ahsalohcin/GP-Team-8-/ihab/GrandPrIEEEE_2017-master/GrandPrIEEEE_2017-master/Natcar Docs/7-controller.pdf

### NATCAR – Background Information

### Steering Control-Loop Design Part I

Prof. Richard Spencer

### Outline

- The feedback-control problem
- PID Controllers
- Kinematic model of car
- Simulated response

### The Feedback Control Problem

- Remember the basic block diagram we had before:
- The “Plant” or “Process” is your car in this project
- The objective in designing the sensing and controller is to make the car follow the course in a well-behaved manner so that it can do so quickly
- You have two loops to design: steering and speed

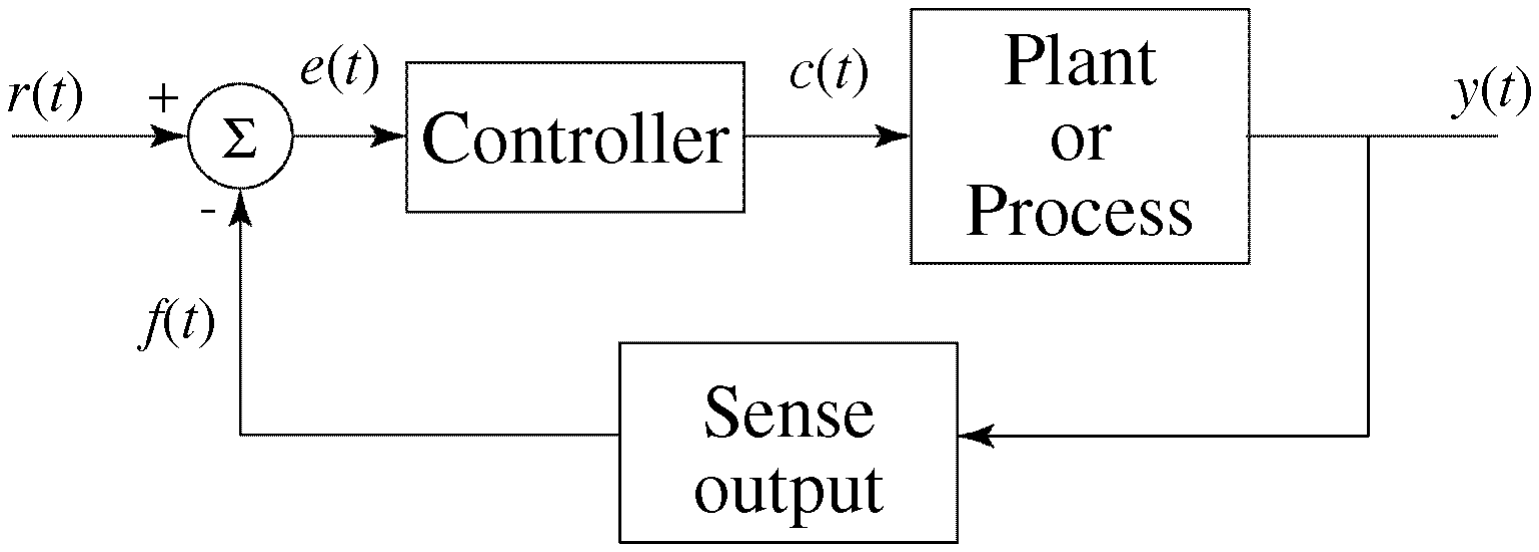
[picture p55: figure]

### Controller Design

- There are many types of controllers used to tailor the response of a control system. EEC157A,B discusses this topic at length.
- We will only examine one very general form for the controller; a Proportional + Derivative + Integral (PID) controller.
- The controller output is simply given by the sum of three terms:
– Proportional;

– Integral;

– Derivative;

( ) | ( ) p ct | ket =
( ) | ( ) pd c t | k T de t dt = | ⎡ | ⎤ ⎣ | ⎦

()

0

()

t
p

i

k
ct | e | d
T = | λλ ∫

### PID Controller

- The controller transfer function is
- The loop gain is then the product of the transfer functions of the controller, the plant and the sensing system.
- Let’s derive a model for our “plant”, which is the car. Then we’ll return to examine the design of an appropriate controller. We will focus here on the steering control loop – it is BY FAR the most important (the fastest car to date had a fixed speed).
() | ( ) ()
1 1 c | p | d

i

Cs
H s | k | sT
E s | sT
⎛ | ⎞
= | = | + | + ⎜ | ⎟ ⎝ | ⎠

### Kinematic Model for the Car

- Because the traction is very good and the tires don’t deform much, we can use a kinematic model (i.e., ignoring mass and force) instead of a full dynamic model for the car.
- We will assume a constant velocity, but the results are fine so long as the velocity doesn't change too rapidly.
- When we have the model in the Laplace domain, we can then build a Matlab (or even SPICE) model for the car and simulate the performance of the car with a given controller design.

- Assume small θ and φ and that the car is moving with constant velocity v. Write equations for the position of the center of the rear axle.
- First:

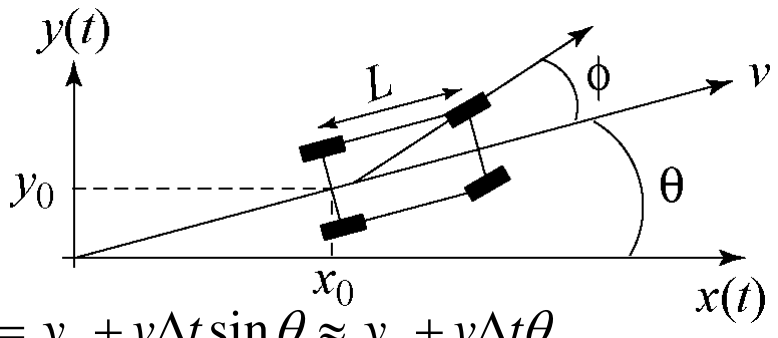
[picture p56: figure]

then,
- Second:
so,
0 | 0 y t | y vt | y vt ( ) | sin Δ = +Δ | ≈ +Δ θ | θ
y dy dt v = | ≈ θ
0 | 0 x( ) | cos Δ = +Δ | ≈ +Δ t | x vt | x vt θ
x = dx dt v ≈

### Kinematic Car Model Continued

This model is
sometimes called
the bicycle model

x0 and y0 are the
positions at t = 0

### Use New Axes in Line with the Car

Assume both the back and front wheels move in the direction they are pointing (can’t be true). We want to find the change in car direction, Δθ. Define a new axis, y’, perpendicular to v

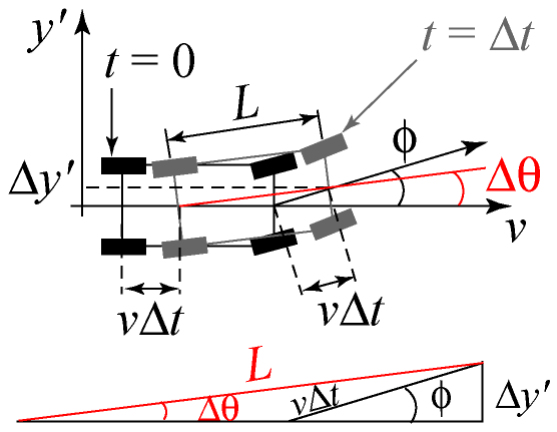
[picture p57: figure]

1 sin

sin

y | y
L | L
y vt | vt
vt
L

θ

φ φ
φ θ
− ⎛ | ⎞ Δ | Δ ′ | ′ Δ= | ≈ ⎜ | ⎟ ⎝ | ⎠
Δ =Δ | ≈Δ ′
Δ Δ≈

- Now write an equation for the y-component of the sensor position (taken to be at the center of the sensor array)

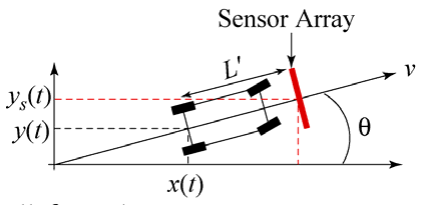
[picture p58: figure]

- Still assuming small θ , we have
- So,
( ) | ( ) | sin
| ()
s y | t | yt L
yt L

θ
θ

Δ= Δ+ ′
≈ Δ+ ′

### Kinematic Car Model Continued

() | () s y | t | yt L | v | L Δ≈ Δ+ | ≈ + ′θ θθ′ | |

### Put the Equations Together

We have | and
Therefore, | and, still assuming v is
constant,

so that, in the Laplace domain we have

s y | v | L ≈+ θ ′θ
| vt
L

φ θ Δ Δ≈

v
L

φ θ ≈

2

s

v | vL y | v | L | L | L
φ | φ θθ | ′ ≈+ | = | + ′ | |
2 | 2
2 | 2
1 | / () | () | () s
v | vL | v | sL v Ys | s | s
Ls | Ls | L | s
⎛ | ⎞ | ⎛⎞ ′ | ⎛ | ⎞ + ′ ≈ | + | Φ= | Φ ⎜ | ⎟ | ⎜⎟⎜ | ⎟ ⎝ | ⎠ | ⎝⎠⎝ | ⎠

### Model the System

The transfer function for the car is

Let’s assume that the servo is linear and model it by a single-pole LP transfer function

The overall model for our plant is then given by

()

2

2

() | 1 | /
()

s
car
Y s | v | sL v H | s
s | L | s
⎛⎞⎛ + ′ ⎞ = | = ⎜⎟⎜ | ⎟ Φ | ⎝⎠⎝ | ⎠

() ()
() 1

s k
Hs
Cs | s φ
φ | ωφ
Φ= | = +

()

| 2

2

() | 1 | /
() 1

s
p
Y s | v | sL v k
Hs
Cs | s | L | s
| φ
ωφ
⎛⎞⎛ + ′ ⎞ = | = | ⎜⎟⎜ | ⎟ + | ⎝⎠⎝ | ⎠

### System Model Continued

- Assume the sensors provide an output proportional
to the deviation from the track so that | .
- We now have a complete block diagram model of our control system.
– ys(t) is the sensor array deviation from the track (in feet) – r(t) is the reference input, which is zero
– T(t) is the racetrack; it provides deviations that the control loop must respond to.
( ) Hs | s s | k =

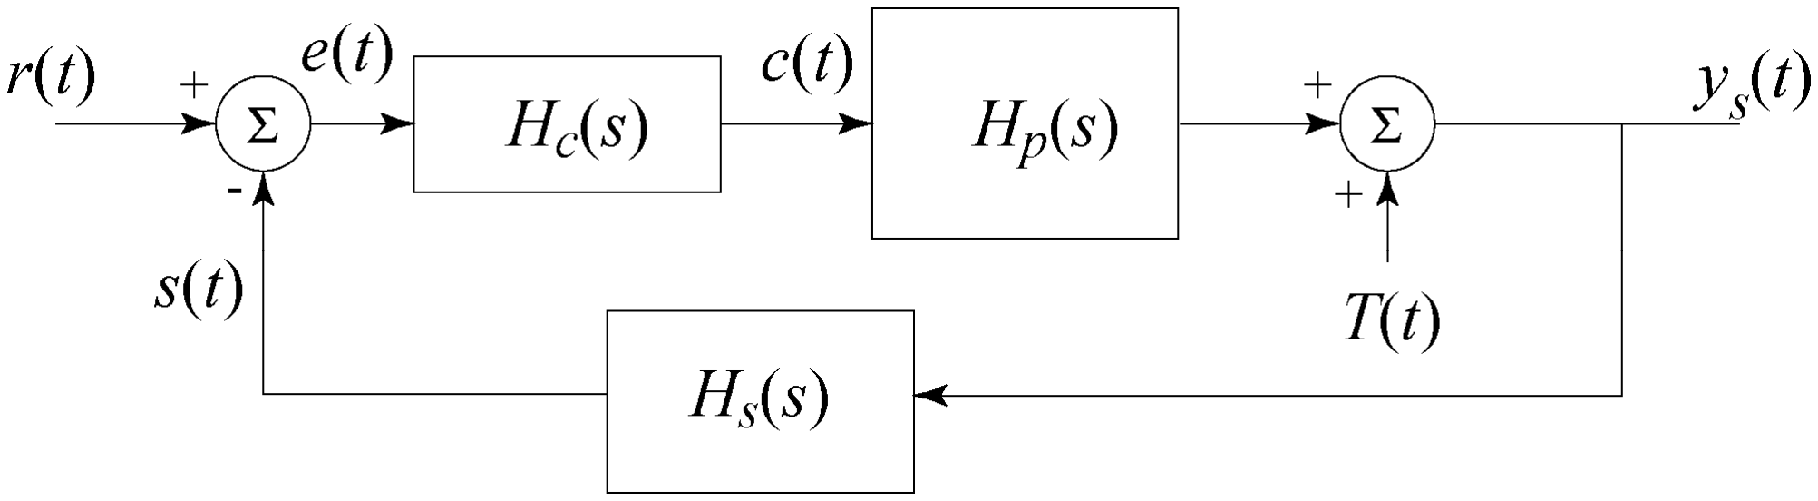
[picture p59: figure]

### System Model Continued

- Since r(t) = 0, we can redraw the loop with the track as the input.

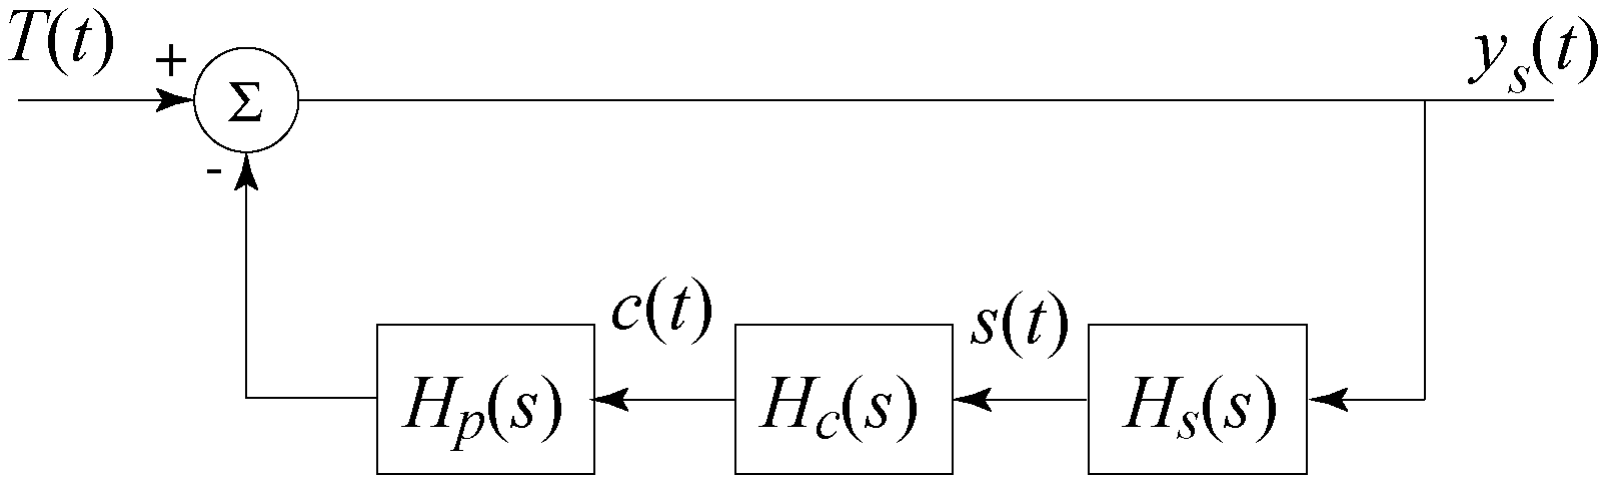
[picture p60: figure]

- Using the equations we’ve derived, we have
( ) ( ) ( ) ( )

2

2

1 | 1 | / 1
1
s | c | p
sp | d
i
Ls | H sH sH s
k | v | sL v k k | sT
sT | s | L | s

φ
ωφ

=
⎛ | ⎞ | ⎛⎞⎛ + ′ ⎞ = | + | + ⎜ | ⎟ | ⎜ ⎜⎟ | ⎟ ⎝ | ⎠ + | ⎝⎠⎝ | ⎠

### System Model; Example Numbers

- Assume the following:
– The sensor gain is one (V/ft)
– The servo gain is π/2 = 1.57 (rad/V)
– The servo bandwidth is 100 rad/sec
– The wheelbase is L = 1 foot and L’ = 1.5 feet
– The velocity is 5 ft/sec
– The controller is proportional only with a gain of one (V/V)
- Let’s use Matlab to generate the Bode plots, a Nyquist plot of L, and the step response for the closed-loop system with a proportional-only controller

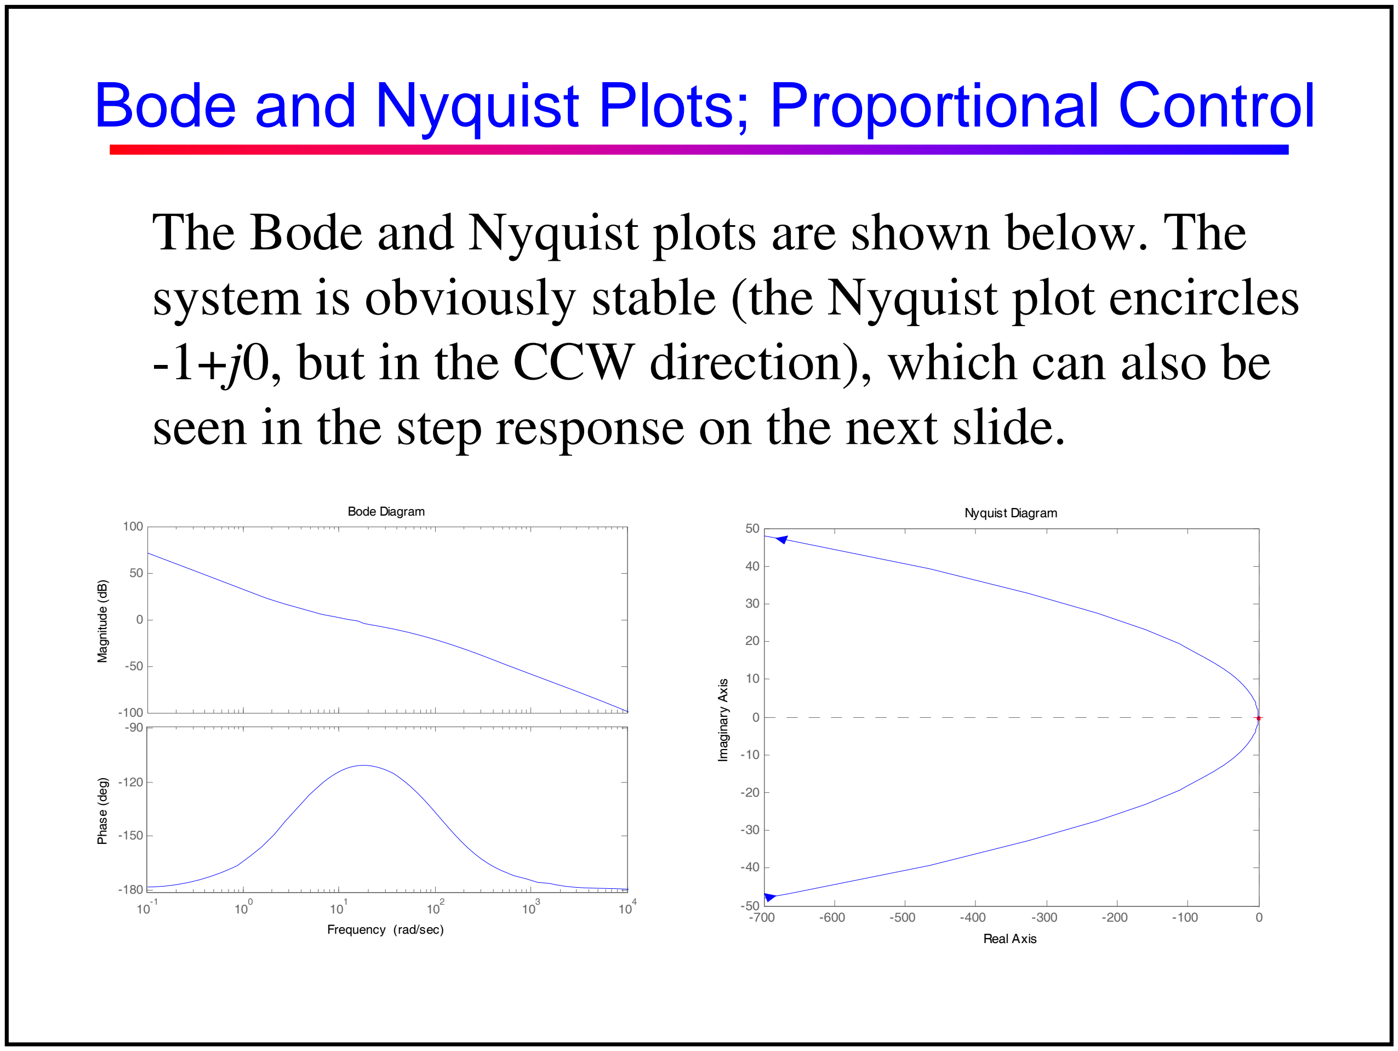
[picture p61: figure]
Magnitude (dB); Phase (deg); Bode Diagram; Frequency (rad/sec); Nyquist Diagram; Real Axis; Imaginary Axis

Bode and Nyquist Plots; Proportional Control

The Bode and Nyquist plots are shown below. The system is obviously stable (the Nyquist plot encircles -1+j0, but in the CCW direction), which can also be seen in the step response on the next slide.

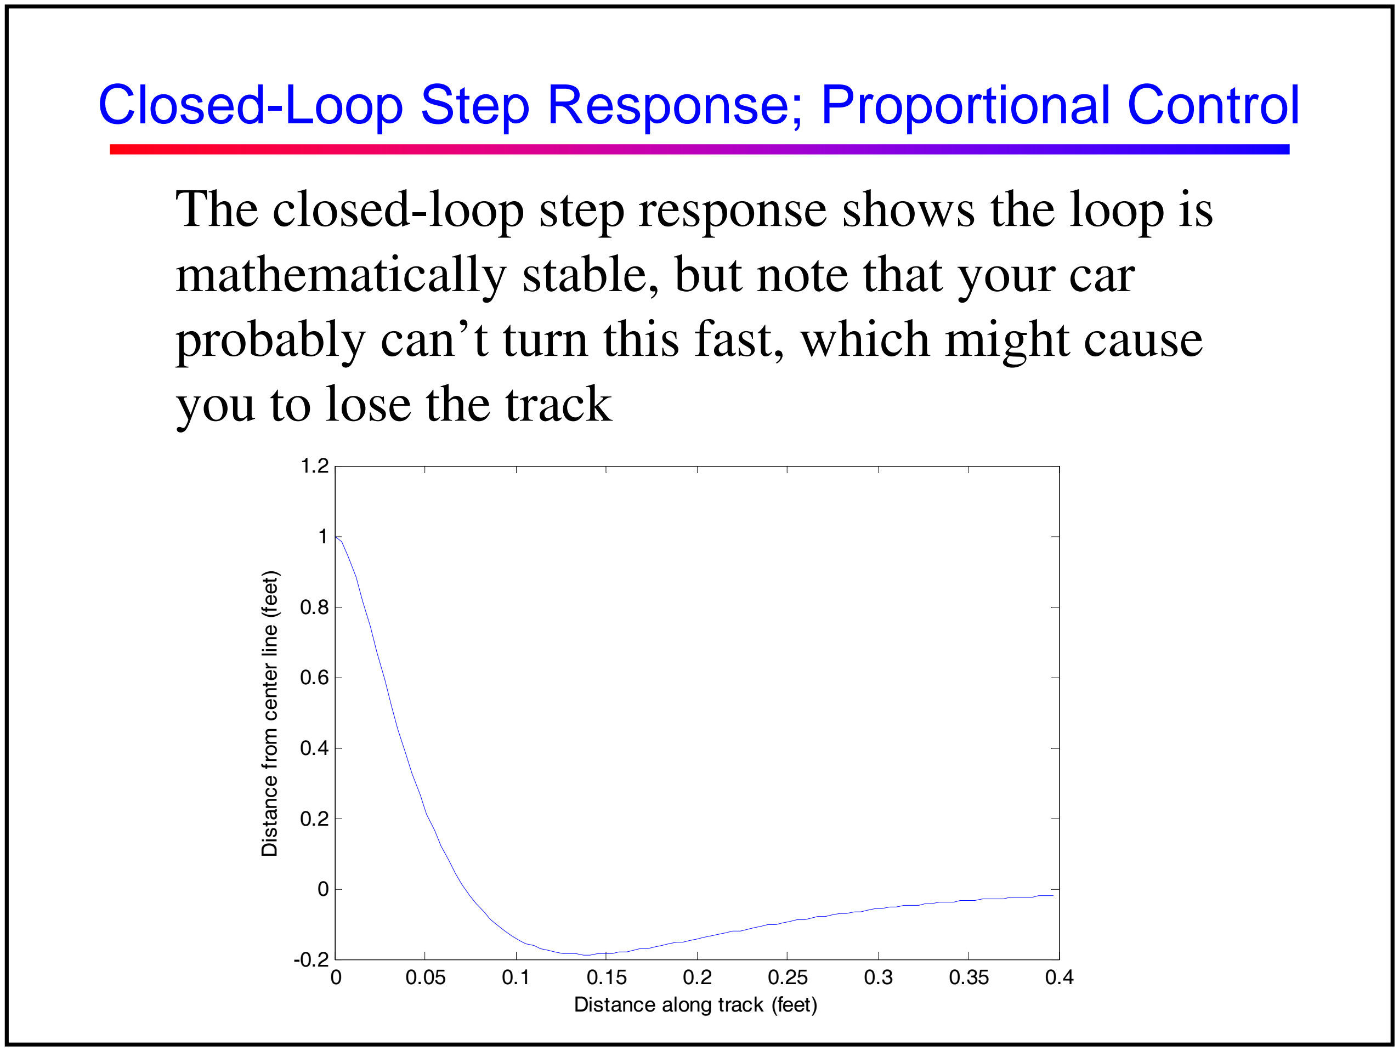
[picture p62: figure]
Closed-Loop Step Response; Proportional Control; you to lose the track; Distance along track (feet); Distance from center line (feet)

The closed-loop step response shows the loop is mathematically stable, but note that your car probably can’t turn this fast, which might cause

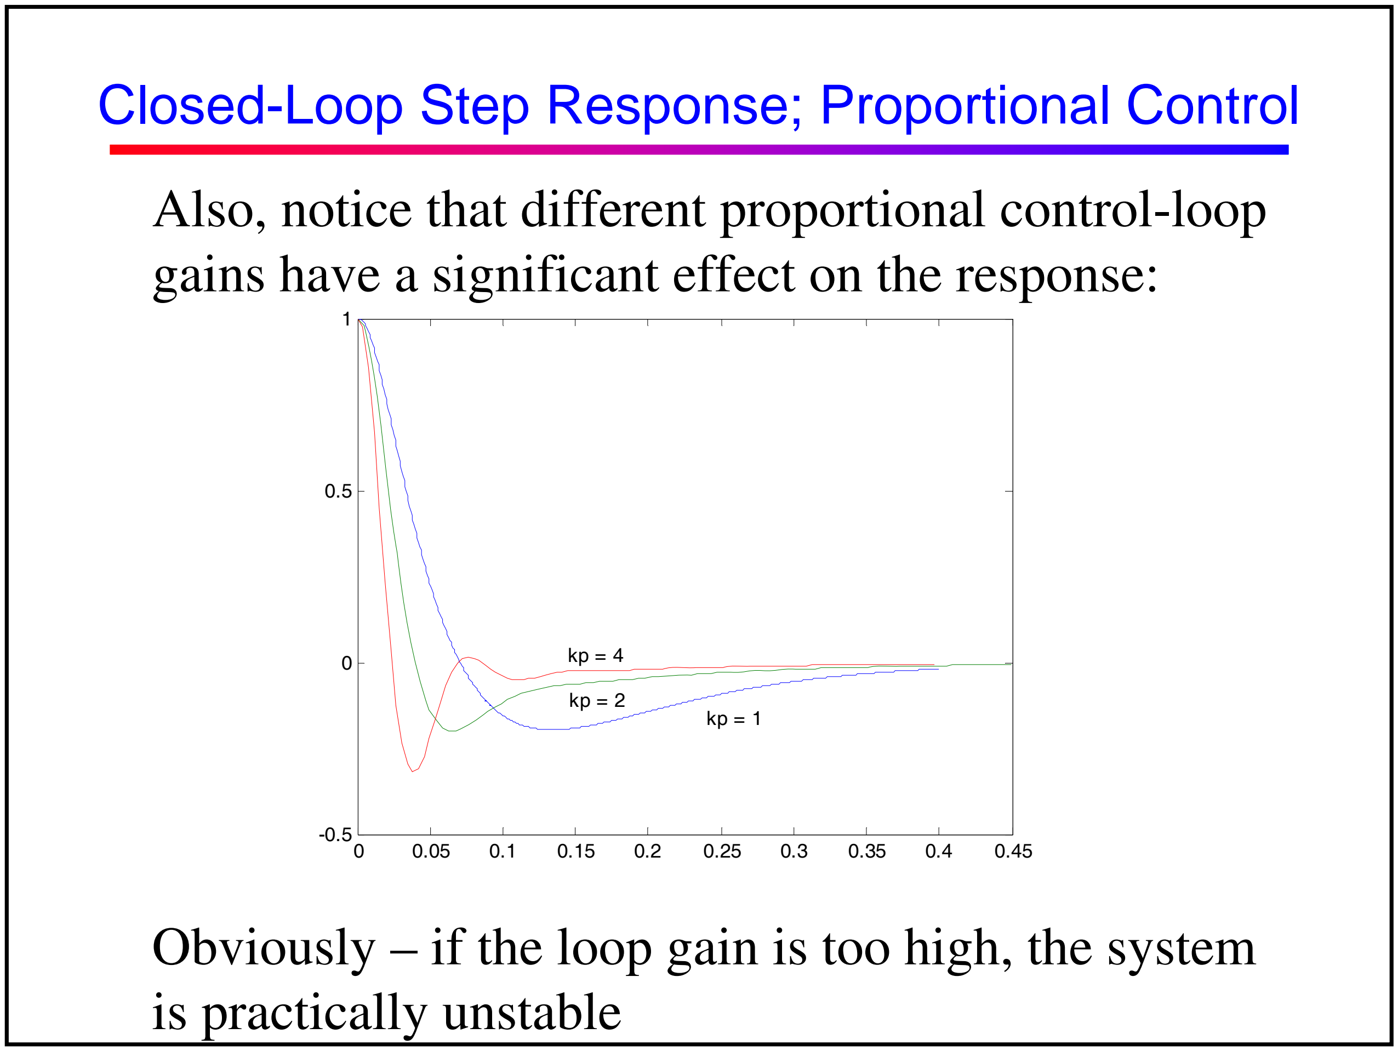
[picture p63: figure]
Closed-Loop Step Response; Proportional Control; is practically unstable

Also, notice that different proportional control-loop gains have a significant effect on the response:

Obviously – if the loop gain is too high, the system

### Re-Consider System Model

- Let’s reconsider our system model and see what we are ignoring
– The servo has a slew-rate limitation

### Servo Slew-Rate Limitation

- Slewing is a nonlinear phenomenon, so we can’t rigorously model it in the Laplace domain
- Nevertheless, servo slewing delays the steering response, and adding delay into the loop makes it less stable
- In addition, the slewing prevents the car from turning as quickly as our simulations sometimes show, which means that your car may run off the track and lose the signal entirely even if the control loop is theoretically stable

### Re-Consider System Model

- Let’s reconsider our system model and see what we are ignoring
– The servo has a slew-rate limitation
– The sensing transfer function may be nonlinear

### Nonlinear Sensing

- If the sensing transfer function is monotonic and reasonably smooth, then nonlinearity does not significantly affect stability
– if it had steps, that might cause problems because it would cause rapid changes in the steering and would drive the servo into a slewing mode more often
– if it was non-monotonic, then negative feedback would become positive feedback wherever the slope of the sensing transfer function changed sign and the loop could enter a local limit cycle

### Re-Consider System Model

- Let’s reconsider our system model and see what we are ignoring
– The servo has a slew-rate limitation
– The sensing transfer function may be nonlinear
– The steering servo is only controlled at discrete times, in other words, the steering angle is actually sampled and held (about every 3 ms)

### Sampling

- The control signal generated by your circuits, c(t), is continuous-time, but it controls a PW modulator and the value is only transferred to the steering servo once every period (about once every 3ms)
- Therefore, the servo functions as a sample-and-hold circuit; that is, it samples c(t) once a period and then holds that value until the next sample arrives
- Let’s consider this intuitively for a moment …

### Sampling Continued

- If the time samples are held, you get a waveform that looks like this

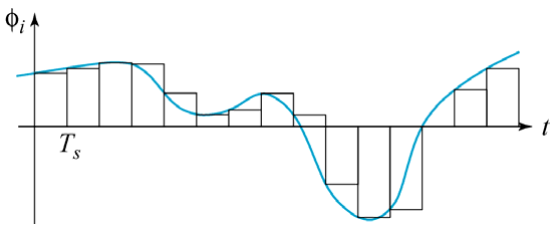
[picture p64: figure]

### Sampling Continued

- If the time samples are held, you get a waveform that looks like this
- Notice that if you reconstruct the original from the sampled-and-held version, it appears delayed!

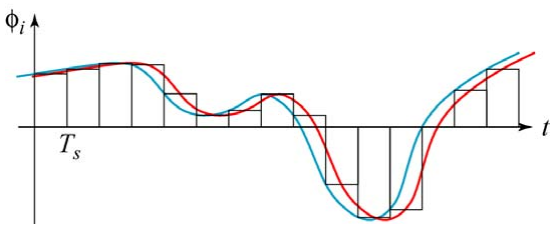
[picture p65: figure]

### Sampling Continued

- Adding delay into the loop is equivalent to adding in extra phase, so it tends to make the loop less stable

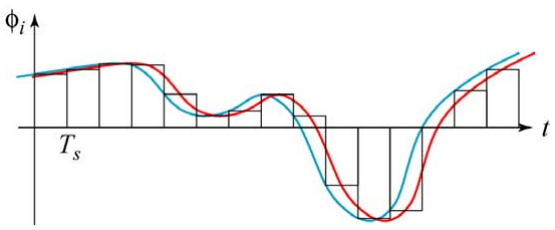
[picture p66: figure]
