ahsalohcin/GP-Team-8-/ihab/GrandPrIEEEE_2017-master/GrandPrIEEEE_2017-master/Natcar Docs/7B-PID-controller.pdf

### NATCAR – Background Information

### Steering Control-Loop Design Part II

Prof. Richard Spencer

### The System Model

Remember that the overall model for our plant is given by

The controller transfer function is

And we assumed the sensors have

()

2

2

() | 1 | /
() 1

s
p
Y s | v | sL v k
Hs
Cs | s | L | s
| φ
ωφ
⎛⎞⎛ + ′ ⎞ = | = | ⎜⎟⎜ | ⎟ + | ⎝⎠⎝ | ⎠
() | 1 1 c | p | d

i

H s | k | sT
sT
⎛ | ⎞
= | + | + ⎜ | ⎟ ⎝ | ⎠
Hs ( ) s s | k =

### The System Model Continued

- Also remember that the servo only samples the control voltage (about every 3ms) and then holds the value until it gets the next sample, so its input is really the sampled-and-held version of the control output, which we showed last time is roughly equivalent to adding some delay (~TS/2) into the loop

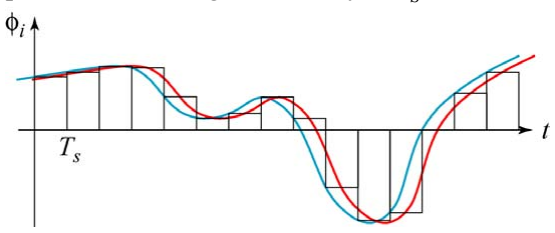
[picture p67: figure]

### Aside on Sampling

- We now want to quickly look at how to model this sample-and-hold operation mathematically
- The sample-and-hold function can be broken down into two separate functions; ideal impulsive sampling followed by a hold function
- Ideal sampling can be described mathematically by multiplying the waveform by a periodic string of impulses s(t):
() | ( | )

k

s t | t kT δ

∞

=−∞

= − ∑

### Sampling Continued

- Therefore, if we sample some waveform x(t) and denote the sampled waveform by x’(t) we find
- The Fourier transform of this infinite comb of impulses, s(t), is itself an infinite comb of
impulses, S(ω):
() | () () | () ( | ) | ( ) ( | )
k | k
x t | x t s t | x t | t kT | x kT t kT δ | δ
∞ | ∞
=−∞ | =−∞
′ = | ⋅ | = | − | = | − ∑ | ∑
2 () | ( | )s

k

S | k
T

π
ω | δω ω

∞

| =−∞
= | − ∑

### Sampling Continued

- Multiplication in the time domain implies convolution in the frequency domain, so we find:
1 | 1 () | () | () | ( | ) 2 | s

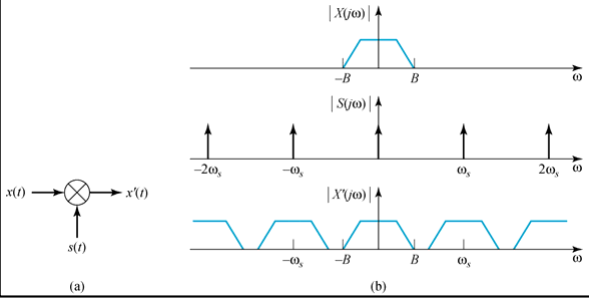
[picture p68: figure]

k

X | X | S | X | k
T
ω | ω | ω | ωω
π

∞

=−∞

′ | = | ∗ | = | − ∑

### Sampling Continued

- So long as the sampling frequency, ωs, is more than twice the signal bandwidth, B, we can recover the signal by low-pass filtering the sampled waveform (B is sometimes called the Nyquist frequency, so ωs must be > 2·ωNyquist)

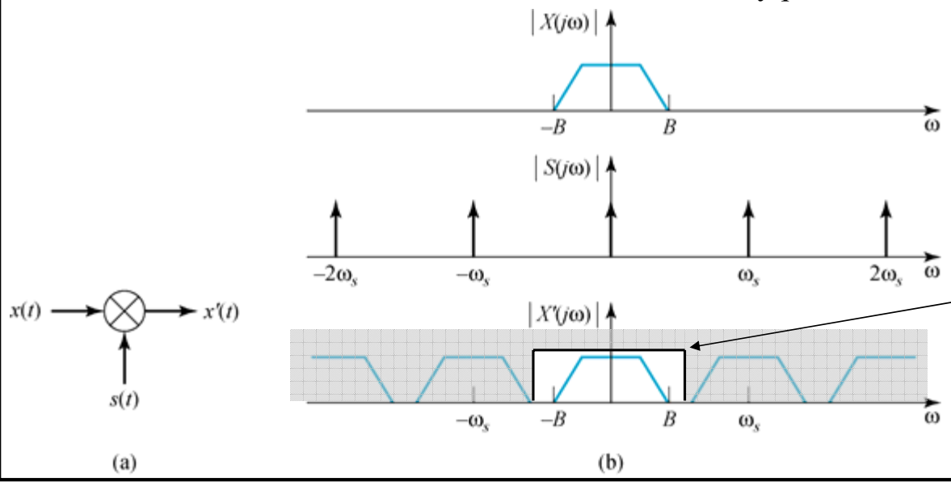
[picture p69: figure]

Ideal LPF

### Sampling Continued

- If the time samples are held, you get a waveform that looks like this:

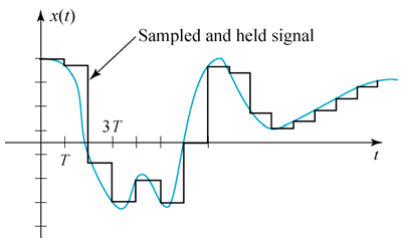
[picture p70: figure]

- This can be generated mathematically by convolving the sampled signal x’(t) with a pulse

### Sampling Continued

- Assuming we have a pulse p(t) defined by
- We find the sampled-and-held waveform is
- The Fourier transform of p(t) is
() | () | () | ( ) ( | ) SH

k

x t | x t p t | x kT p t kT

∞

=−∞

= | ∗ | = | − ′ | ∑
0; | 0 or () | 1;0
t | tT
pt | tT
⎧ | < | > = ⎨
⎩ | <<

0

1 ( ) | ()
T j t | jT
jt | e | e P | e p t dt | j | j
ω | ω
ω ω
ω | ω
∞ | − | −
−

−∞

⎡ | ⎤ − | − = | = | = ⎢ | ⎥ ⎣ | ⎦ ∫

### Sampling Continued

- We had
- And we had
- Therefore, their spectra are multiplied in the frequency domain and we have
() | () | () | ( ) ( | ) SH

k

x t | x t p t | x kT p t kT

∞

=−∞

= | ∗ | = | − ′ | ∑
() | () () X | X | P SH ω = ′ ω | ω ⋅

1 ()

j T
e P
j

ω
ω
ω

− − =

### Sampling Continued

- Note that
- And we had
2 | 2 | 2 | 2
2 | 2
1 | 2 | 2 ( ) | sin 2 | 2

sin
2 | sinc
2
2
T | T | T | T j | j | j | j jT
T | T j | j
e | e | e | e | e | T P
j | | | j
| T
T Te | Te T
ω | ω | ω | ω
ω
ω | ω

ω
ω
ω | ω | ω

ω
ω
ω
− | − | − −
− | −
⎛ | ⎞ − | − ⎜ | ⎟ = | = | = ⎜ | ⎟
⎝ | | | | | | ⎠
= | =
1 () | ( | )s

k

X | X | k
T
ω | ωω

∞

=−∞

′ | = | − ∑

### Sampling Continued

- Therefore,

2

2

1 ( ) | ( ) ( ) | ( | ) | sinc 2
sinc | ( | ) 2

T j

SH | s
k
T j

s
k
T X | X | P | X | k | Te
T
T e | X | k

ω

ω

ω
ω | ω ω | ωω
| ω | ωω
∞ | −

=−∞
∞ −

=−∞

⎡ | ⎤ = | ⋅ | = | − ′ | ⎢ | ⎥ ⎣ | ⎦
= | −

∑
∑

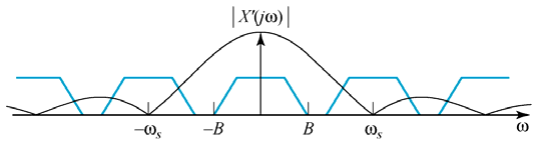
[picture p71: figure]

### Sampling Continued

- Note that if we focus on the region around zero (because we will low-pass filter the output), we can restrict our attention to the k = 0 term,
1 () | () () | ( | ) ()
| 1 ( ) ( ) | ( ) ( ) for | 0
SH | s
k
X | X | P | X | k | P
T
X | P | X | P | k
| T
ω | ω | ω | ωω | ω
ωω | ω ω

∞

=−∞

⎡ | ⎤ = | ⋅ | = | − ′ | ⎢ | ⎥ ⎣ | ⎦
= | ≡ | = ′

∑

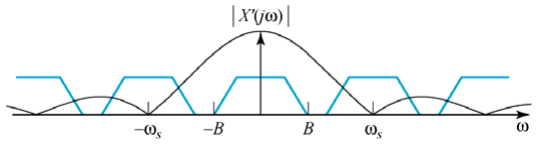
[picture p72: figure]

### Sampling Continued

- In other words, the sample-and-hold transfer function has a strange low-pass transfer charac-teristic that we must allow for in our simulations
- We do not need to model the actual sampling operation if we use a continuous-time model and assume that the sampling frequency is high enough (since we can perfectly reconstruct the signal)
- In the Laplace domain, we have
- This particular type of hold is called a zero-order hold (higher-order holds do a better job of interpolating between adjacent samples)

1 ()

sT
e Ps
sT

− − ′ =

### Simulation Model for the Loop

- But, we can’t enter the zero-order hold directly into Matlab as a transfer function – it won’t allow the perfect delay represented by the exponential (unless we do a discrete-time approximation to the entire control system in the z domain)
- An alternative to using MATLAB is to model the loop using SPICE – this method also has the advantage of allowing us to model nonlinearities
- The Laplace blocks available in PSPICE work in the frequency domain, but not in the time domain – so we must use controlled sources and elements to build up a behavioral model of the system

### PSPICE Car Model

- The transfer function for the car is

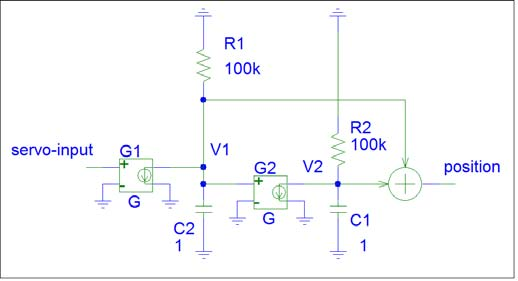
[picture p73: figure]

- We can model this in PSPICE with this circuit
2 | 2
2 | 2
1 | / () | () | () s
v | vL | v | sL v Ys | s | s
Ls | Ls | L | s
⎛ | ⎞ | ⎛⎞ ′ | ⎛ | ⎞ + ′ ≈ | + | Φ= | Φ ⎜ | ⎟ | ⎜⎟⎜ | ⎟ ⎝ | ⎠ | ⎝⎠⎝ | ⎠

### PSPICE Car Model Continued

- Ignore R1 and R2 at first – PSPICE requires them, but they don’t affect the operation much. So

and

- Therefore,

1
1
1
() | () in
G Vs | V s
sC
− = | 2 | 12
2 | 1 | 2
| 2 | 12
() | () | () in
G | GG V s | Vs | V s
sC | s C C
− = | =
12 | 1
1 | 2 | 2 () | () | () | () o | in
GG | G V s Vs V s | V s
s | s
⎛ | ⎞ = | + | = | − ⎜ | ⎟ ⎝ | ⎠

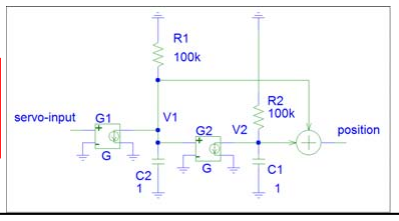
[picture p74: figure]

Note that both
capacitors are
1 Farad

### PSPICE Car Model Continued

- Setting Vin = Φ and Vo = Y, we have
- which requires | and 1

vL G
L

− ′ =

2
12 | 1
2 | 2 () | () | () s
v | vL | G G | G Ys | s | s
Ls | Ls | s | s
⎛ | ⎞′ | ⎛ | ⎞ ≈ | + | Φ= | − | Φ ⎜ | ⎟ | ⎜ | ⎟ ⎝ | ⎠ | ⎝ | ⎠

2

v G
L

− = ′

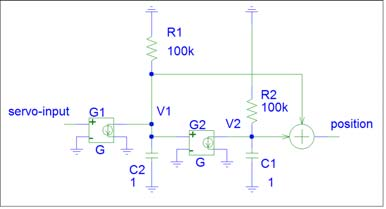
[picture p75: figure]

### PSPICE Servo Model

- The servo can be modeled in PSPICE as shown below – this model includes the servo slew rate, small-signal bandwidth and limits
- The first block has negative feedback, so

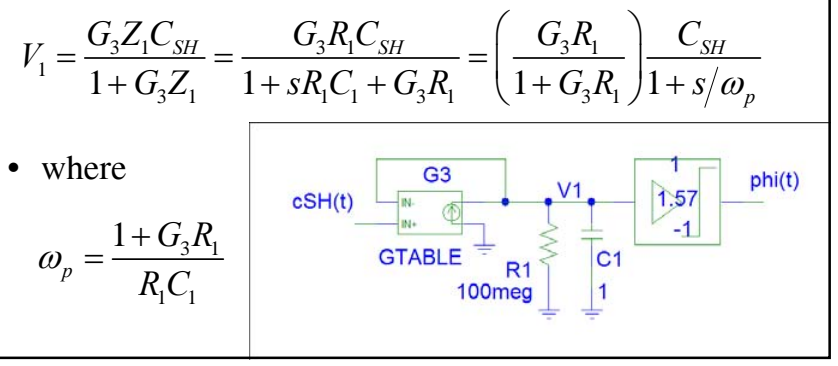
[picture p76: figure]
• where

### PSPICE Servo Model

- The slew rate is set by the maximum current available out of the GTABLE block; assuming it all flows into C1, the maximum rate of change of V1 is
- The steering limits are given by the voltage limit block, and the overall DC gain is also set by this block since we set
1 | max
max | 1
dV | I
dt | C =

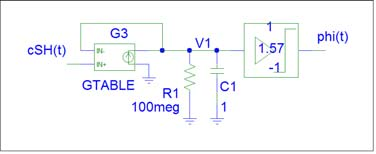
[picture p77: figure]

31

31

1
1

GR
GR
⎛ | ⎞
⎜ | ⎟ ≈
⎝ | ⎠ +

### PSPICE Zero-Order Hold Model

- The zero-order hold can be modeled using an ideal transmission line to provide the delay
- The transmission line must be terminated properly to prevent reflections – I used a 100Ω line with a 3ms delay (T1 in the schematic)
- The integrator block provides the 1/s term
- The input gain includes a factor of 2 to allow for the divider formed by R2 and the line as well as the 1/T term

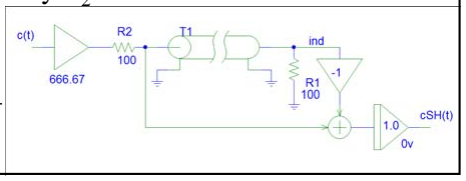
[picture p78: figure]

() | 1 () ()
sT Cs | e SH | Ps
C s | sT
− − = | = ′

### PSPICE Controller Model

- I modeled a PD controller as shown below
- The input gain block sets kp (10 in the schematic)
- The current in C1 is the derivative of kp·s(t), so the gain of the H1 block sets Td
- The output is the sum of the derivative and
proportional terms: c t | k | sT s t () | 1 | () = p | d ( + | )

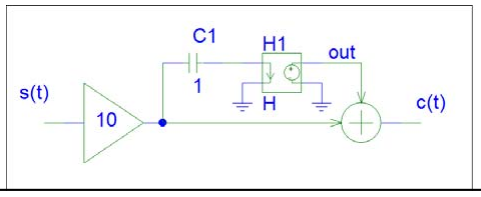
[picture p79: figure]

### Complete PSPICE Model

- The complete PSPICE model for the feedback loop is shown below
- The sensors are modeled by a gain block and the track by an independent source
- The gain of −1 is used to make the summer take the difference between Vin and the car’s position

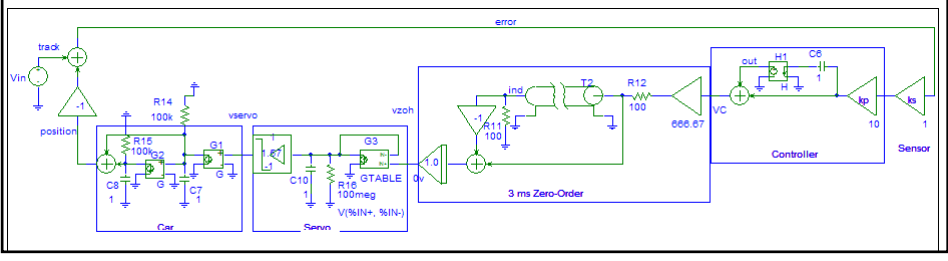
[picture p80: figure]

### System Model; Example Numbers

- Assume the following:
– The sensor gain is one (V/ft)
– The servo gain is π/2 = 1.57 (rad/V)
– The servo has a bandwidth of 100 rad/sec, a slew rate of 20 rad/sec (120º change in 0.1 sec) and limits of ±1 V (±60º) – The wheelbase is L = 1 foot and L′ = 1.5 feet
- Let’s use our PSPICE model to examine the step response for different velocities and controllers WARNING! You have to set the maximum step size in the transient simulations to a small value (I used 0.005ms most everywhere) and, perhaps, reduce the charge tolerance or you will not get accurate step responses

### Step Response

- Here is the step response (6 in. step) with kp = 1, Td = 0 s and v = 1 ft/s

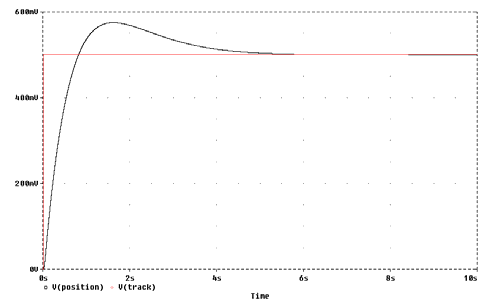
[picture p81: figure]

1 s = 1 foot

1V = 1 ft.

### Step Response

- Here is the step response (6 in. step) with kp = 10, Td = 0 s and v = 1 ft/s. Note the change in x axis scale and that this has less overshoot than kp = 1!

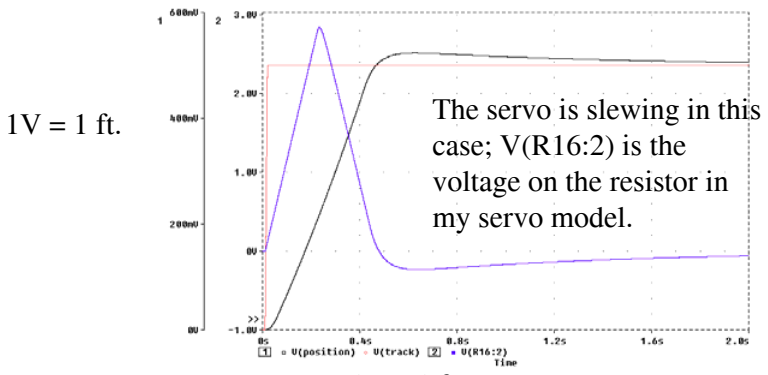
[picture p82: figure]
The servo is slewing in this; case; V(R16:2) is the voltage on the resistor in my servo model.

1 s = 1 foot

### Step Response

- Here is the step response (6 in. step) with kp = 1, Td = 0 s and v = 5 ft/s

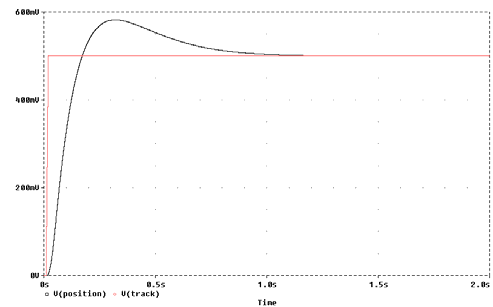
[picture p83: figure]

200 ms = 1 foot

1V = 1 ft.

### Step Response

- Here is the step response (6 in. step) with kp = 10, Td = 0 s and v = 5 ft/s. The servo is again slewing. The loop is, in practice, unstable.

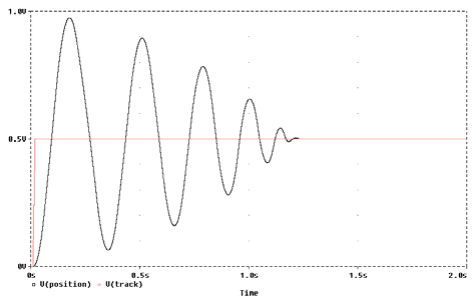
[picture p84: figure]

200 ms = 1 foot

1V = 1 ft.

### Step Response

- Here is the step response (6 in. step) with kp = 10, Td = 0.3 s and v = 5 ft/s. The derivative has helped a lot!

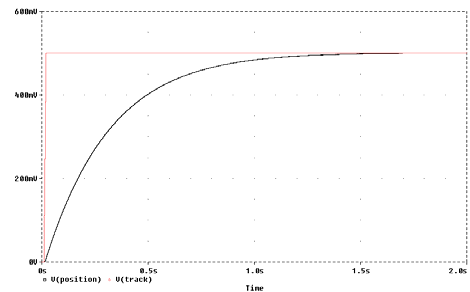
[picture p85: figure]

200 ms = 1 foot

1V = 1 ft.

### Step Response

- Here is the step response (6 in. step) with kp = 1, Td = 0 s and v = 10 ft/s

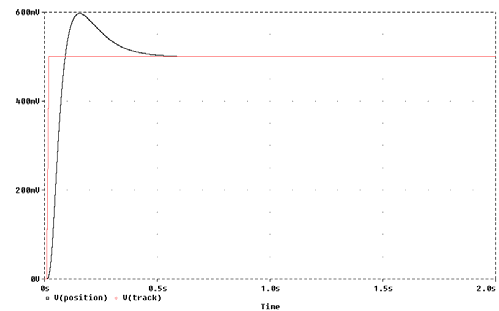
[picture p86: figure]

100 ms = 1 foot

1V = 1 ft.

### Step Response

- Here is the step response (6 in. step) with kp = 10, Td = 0 s and v = 10 ft/s. The loop is unstable here!

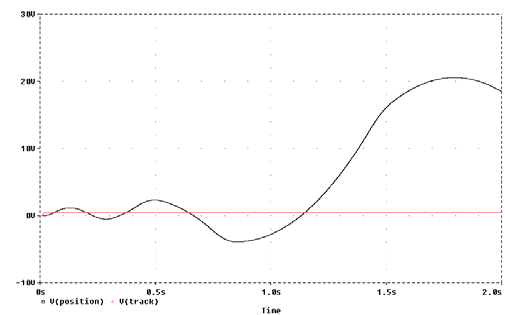
[picture p87: figure]

100 ms = 1 foot

1V = 1 ft.

### Step Response

- Here is the step response (6 in. step) with kp = 10, Td = 0.3 s and v = 10 ft/s. The derivative has again cured the instability.

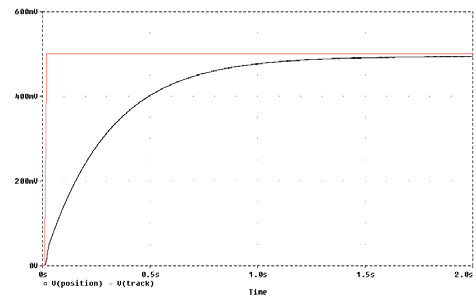
[picture p88: figure]

100 ms = 1 foot

1V = 1 ft.

### Bode Plots

- You can look at the Bode plots, but because of the nonlinearity in the servo and the fact that the phase is not monotonically non-decreasing in magnitude, the results are of questionable value and we will not use them
- PSPICE will not plot a Nyquist plot
