ahsalohcin/GP-Team-8-/ihab/GrandPrIEEEE_2017-master/GrandPrIEEEE_2017-master/Sensing/Magnetic Sensing/Magnetic Sensing Notes.pdf

# Some Notes on Magnetic Field Sensing for National Semiconductor’s Natcar Race

by

# Shane Cantrell

Primary Sources of Information University Physics: Models and Applications by Crummett and Western
and
Shane Cantrell’s fallible brain cells

For an infinitely long, straight wire, the magnetic field B at a point near the field is the following:

B =

0I
2y
0 = 4 10

−7N/A
2
From this we can see that the magnitude of the magnetic field induced by the current through the wire is inversely proportional to the distance the point is from the wire (when the wire is infinitely long and straight).

Using Faraday’s law of induction, we can then find out how this magnetic field can be detected using inductors (solenoids).
= −

dB
dt
B = B dA
Notice that | is the magnetic flux through a single loop and that the electromagnetic field is
B |
only generated by a change in the magnetic flux over time. (This is the reason why an AC current source is used for this project instead of a DC current source.) From this formula, the current generated in a solenoid can be calculated when the magnetic flux is homogeneous over the inside loop.
I =

Nr

2 dB
dt
R
R is the resistance within the solenoid, and N is the number of turns.

y

I | I

B

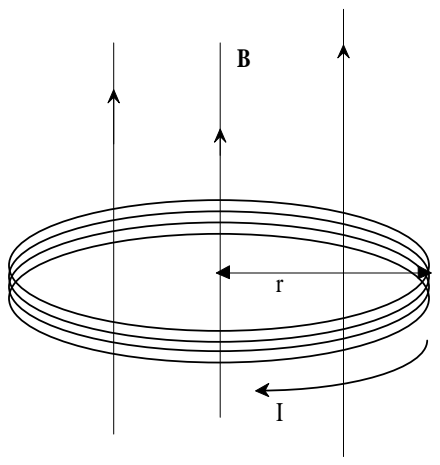
[picture p89: figure]

Now that you have had a really quick review, I will go over some design samples.

Large horizontal sensor that are close to the floor.

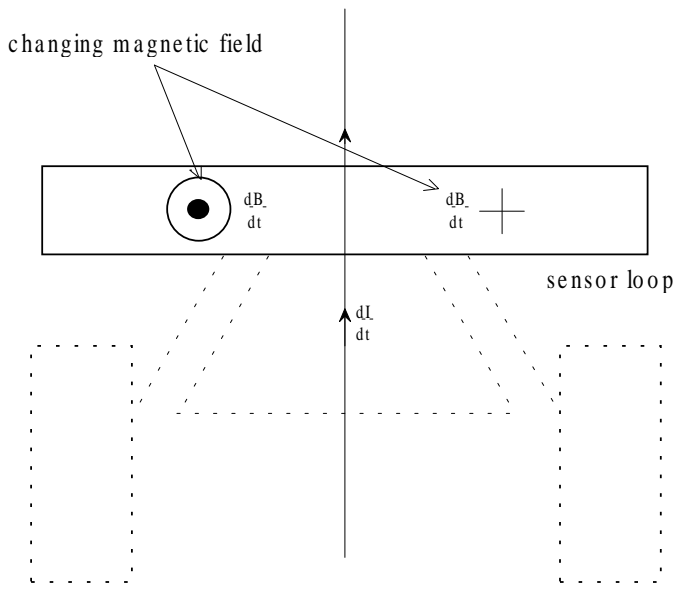
[picture p90: figure]
s e nso r lo o p; c ha nging m a gne tic fie ld

The first design has a long, rectangular loop of wire which rests on the ground in front of the car. When the car is centered around the line (as shown above), the amount of flux going through the loop sums to zero and the sensor sees a value of zero. If, as shown in the picture below, the car is slightly to the left of the wire, there will be more magnetic flux on one side than

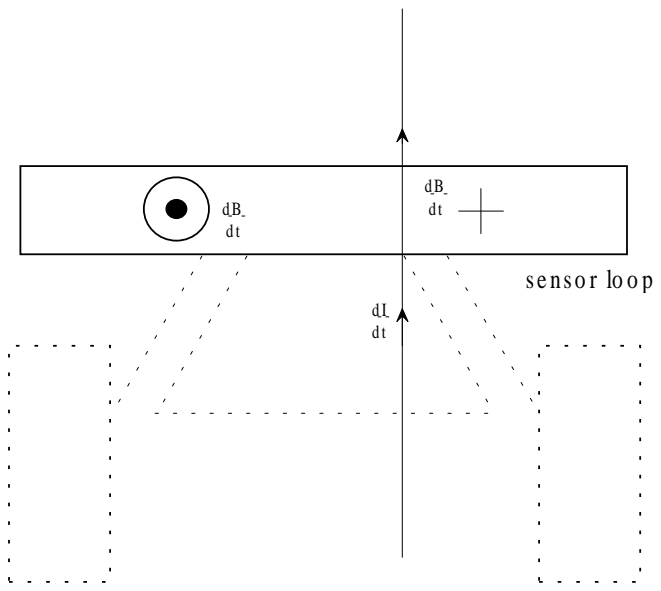
[picture p91: figure]

the other. Unfortunately, the track can be slanted with respect to the car such that the flux is equal on both sides. This shows that even more than one sensor is needed for detecting angle. In addition, the car will be unable to tell which way to turn even with a second, similar sensor

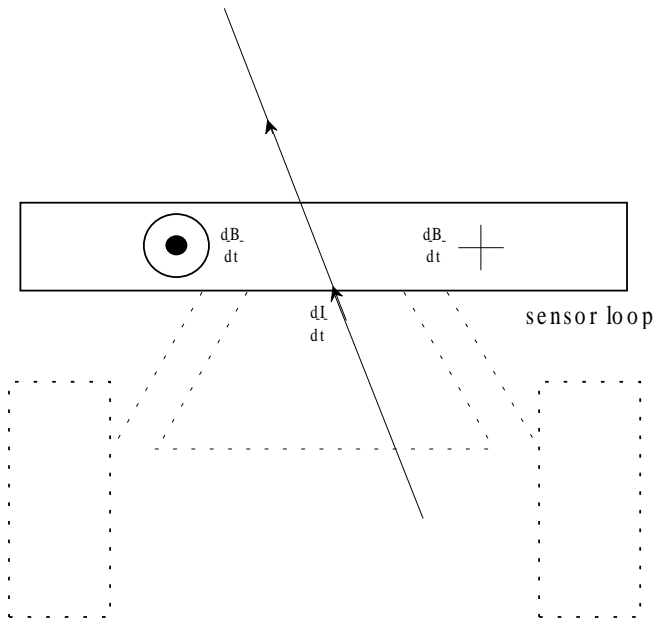
[picture p92: figure]

because without a third sensor to give the car a reference signal, there will be no way to distinguish the left side from the right side even though the signals produced by each side would be out of phase by .

Circular sensors that are flat against the floor.
This method might be easier to implement because inductors are already circular inductors, but there are also other features that are worth mentioning. First of all, it is easier to

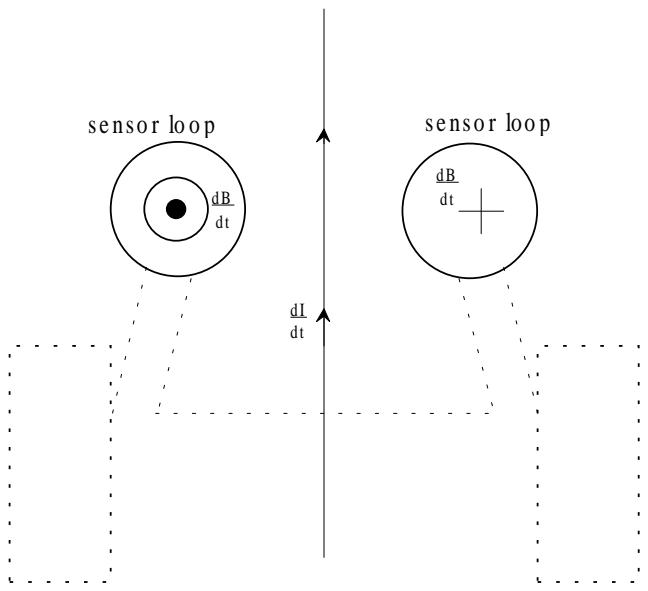
[picture p93: figure]
s e nso r lo o p; s e nso r loo p

tell which side of the wire your car is on; the sensor with the largest magnetic flux will usually be closest to the wire. This, unfortunately, will not be true when the wire passes beneath the sensor because, as in the case of the previous example, the amount of flux going up, through the loop

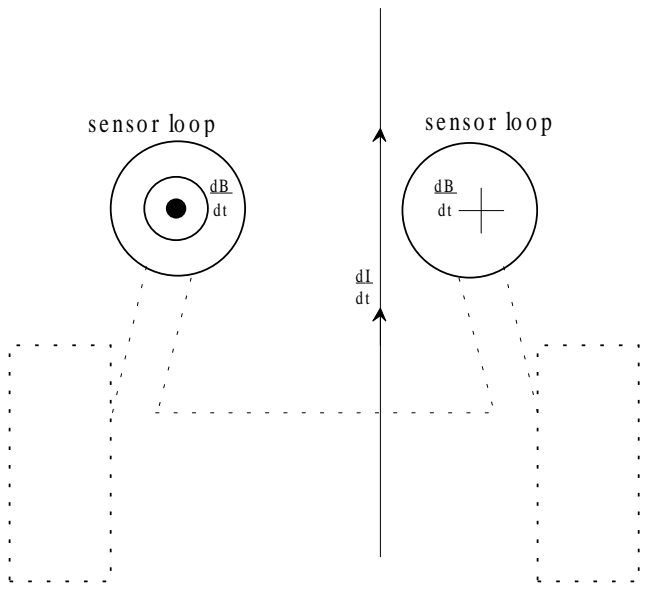
[picture p94: figure]
s e nso r lo o p

will be canceling with the flux going down, through the loop. This will cause the total magnetic flux to drop quickly as the loop passes over the wire. Of course, once the sensor has passed over

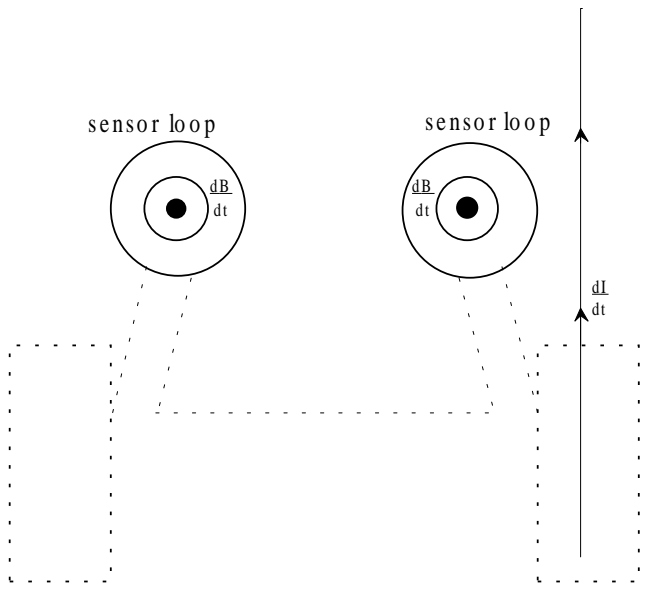
[picture p95: figure]
s e nso r lo o p

the loop, it will be possible to determine that the car is no longer in the middle of the track because the signals will no longer be out of phase as shown in the picture above. With only a pair of these sensors, the angle of the car can not be detected, so it is probably best if two additional sensors are added as shown on the next page.

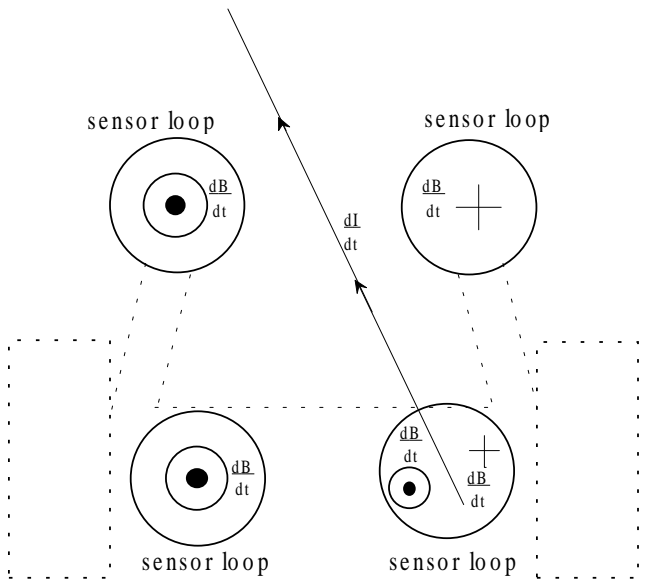
[picture p96: figure]
s e nso r lo o p; s e nso r lo op

Standard, horizontally aligned sensors that are elevated.

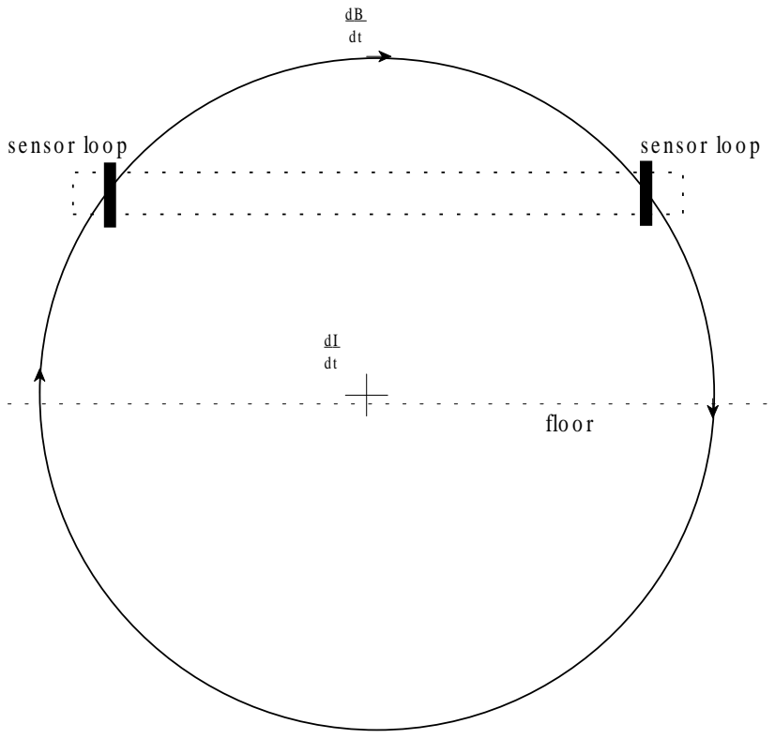
[picture p97: figure]
flo o r

Elevated sensors are one of the most popular orientations for the Natcar race. I think that this is because the sensors do not pass through a null area like the one I described for the previous design; at least when they are orientated as shown above, the signal will not completely die out until changing magnetic field becomes too weak to be detected. Unfortunately, this method is also less efficient because, as shown below, only the portion of the field perpendicular to each coil is actually detected and the rest is lost. If you look at the picture above and the one on the next page, it is apparent that the total field is only detected when the sensor is directly above the wire.

a c tua l

s e ns e d

s e ns o r lo o p

dB
d t

dB
d t

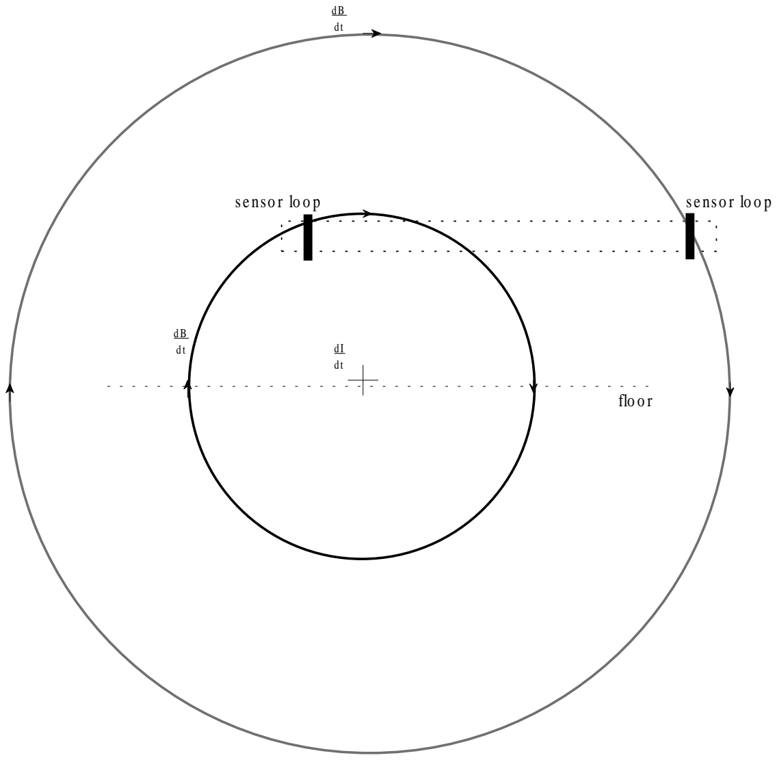
[picture p98: figure]
s e nso r lo o p; flo o r

Notice that not only is the field reduced because of distance, but the percentage of the field is reduced when far from the wire because a smaller amount of the field is perpendicular to the loops.

Further designs.
This information should help you figure out unique locations and orientations that will maximize the stability of your car and allow you to beat those contestants with less understanding. :-)
