ahsalohcin/GP-Team-8-/ihab/GrandPrIEEEE_2017-master/GrandPrIEEEE_2017-master/Sensing/Magnetic Sensing/op-amps.pdf

# Some Notes on Operational Amplifier Based Circuits

by

# Shane Cantrell

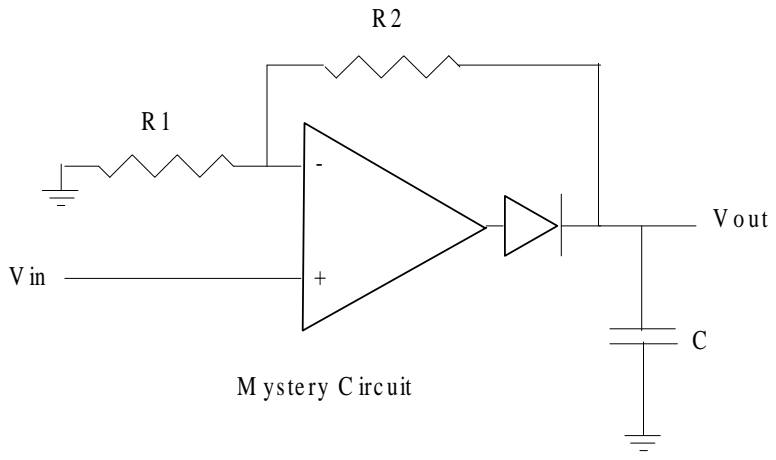
[picture p99: figure]
M yste ry C irc uit

Ideal Operational Amplifiers
Ideal operational amplifiers have infinite gain. If the voltage at the + terminal is larger than the voltage at the - terminal then the output voltage will increase until it reaches the positive power supply. Likewise, if the voltage at the + terminal is smaller than the voltage at the -terminal then the output voltage will decrease until it reaches the negative power supply. Of course, if both terminals are equal, the output will no longer be driven by the op amp. These characteristics allow feedback to be used in order to drive the output of the op amp to a useful value, and, for that reason, all of the circuits that I will be discussing use feedback.

Non Inverting Amplifier
Non inverting amplifiers are very powerful because you can amplify a signal without having a negative rail (depending on the op amp’s specifications). When a voltage is applied to Vin, Vout begins to rise because
of the infinite amplification. This
rising voltage is consequently
applied across the voltage divider of R1 and R2 in such a way that the voltage at the negative terminal of the op amp begins to rise as well. Once the voltage at the negative terminal has reached the same value as the positive terminal, the amplification stops and Vout remains constant. If for
some reason the output voltage is
pushed further up, the voltage at

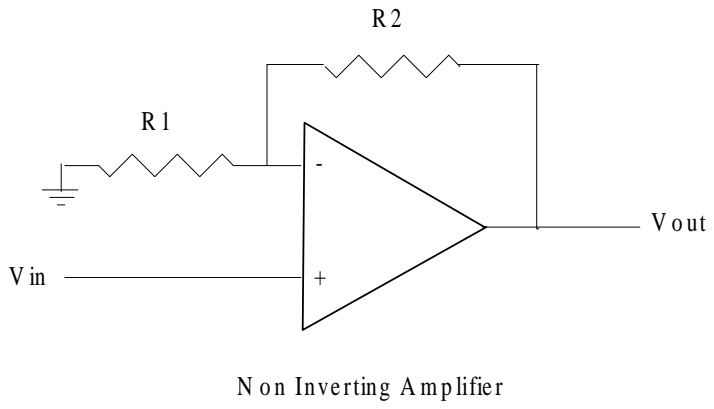
[picture p100: figure]
N o n Inve rting A m p lifie r

R1 will go up causing the op amp to have a negative voltage across it and pull Vout back down again. The formula expressing the ideal Vout is
Vin(

R1+R2
R1

)

Non Inverting Peak Detector Peak detectors allow
you to determine the highest voltage value that a signal produces over a period of time. The one shown here does not do precisely this, but for many slowly varying signals it is good enough. The diode
located at the output of the op amp allows the op amp to add charge to the capacitor C while not allowing it to discharge the capacitor. Because of this, Vout will rise until both the -

V in | +

S im p le P e a k D e te c to r

R | C V o ut

and + terminals of the op amp are equal. Then, if Vin drops, the op amp will no longer be pumping charge into the capacitor, and the resistor R will allow charge to slowly escape and the voltage at Vout to drop. R and C must be picked based on how fast you want Vout to drop after detecting a peak.

Inverting Amplifier
Inverting amplifiers invert your signal and, as a result, require a negative power supply

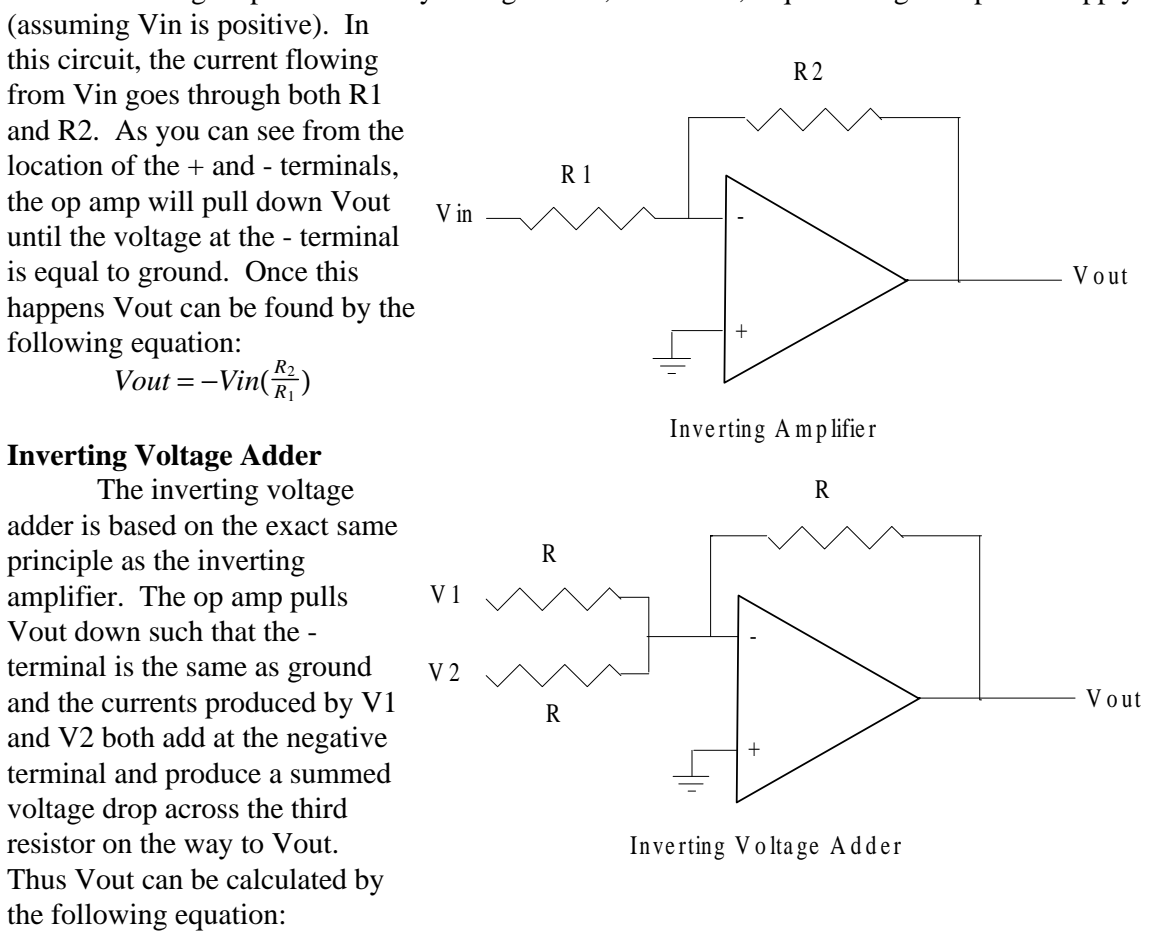
[picture p101: figure]
(assuming Vin is positive). In this circuit, the current flowing from Vin goes through both R1 and R2. As you can see from the location of the + and - terminals, the op amp will pull down Vout until the voltage at the - terminal is equal to ground. Once this happens Vout can be found by the following equation: Vout = −Vin(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

Thus Vout can be calculated by

Vout = −(V1 + V2)
Additional voltage inputs can also be tied to the - terminal if necessary.
