ahsalohcin/GP-Team-8-/ihab/GrandPrIEEEE_2017-master/GrandPrIEEEE_2017-master/Natcar Docs/6-feedback.pdf

### NATCAR – Background Information

### Feedback & Control Theory

Prof. Richard Spencer

### Outline

- Negative feedback
– Basic principle
– Control loop
- Stability of negative feedback loop – Loop gain and phase
– Nyquist plots
– Gain and phase margins
- Step responses (stable and unstable)
- Root-Locus Plots

### Negative Feedback

- Negative feedback was invented by Harold Black in 1927, but is ubiquitous in biological and other natural systems as well as in electronics.
- Negative feedback amplifiers are covered in EEC110B, feedback control is covered in detail in EEC157A-B.
- Basic principle: If the output is supposed to be a scaled replica of the input, then you can take a fraction of the output and compare it with the input to generate an error. This error can be used to force the output to be closer to what it should be.

### Negative Feedback Amplifier

Consider a negative feedback amplifier first:

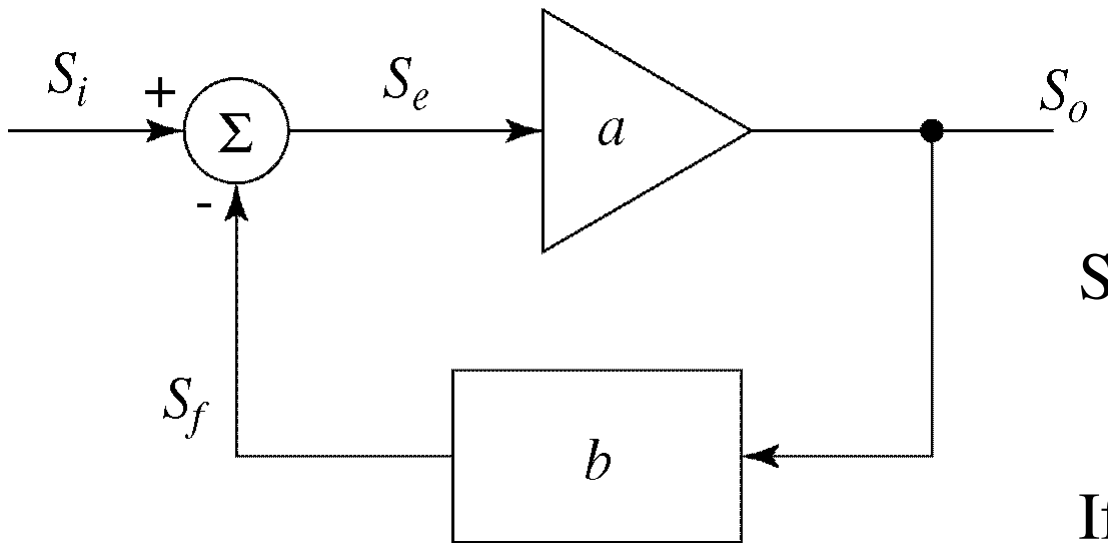
[picture p112: figure]

- For example; if b = 0.1, A ≈ 10 so long as a >>
10. The exact value of a doesn’t matter very much.
- If ab = −1 though, the transfer function blows up and the output can be finite with no input. We’ll come back to this point in a moment.

Solving yields,

( | ) ( | ) o | e | i | f | i | o S | aS | a S S | a S bS = | = | − | = | −

1

o

i

S | a A
S | ab = | = +

1 A
b

If ab >> 1, then ≈

### Negative Feedback Amplifier

Examine the magnitude of the error term:

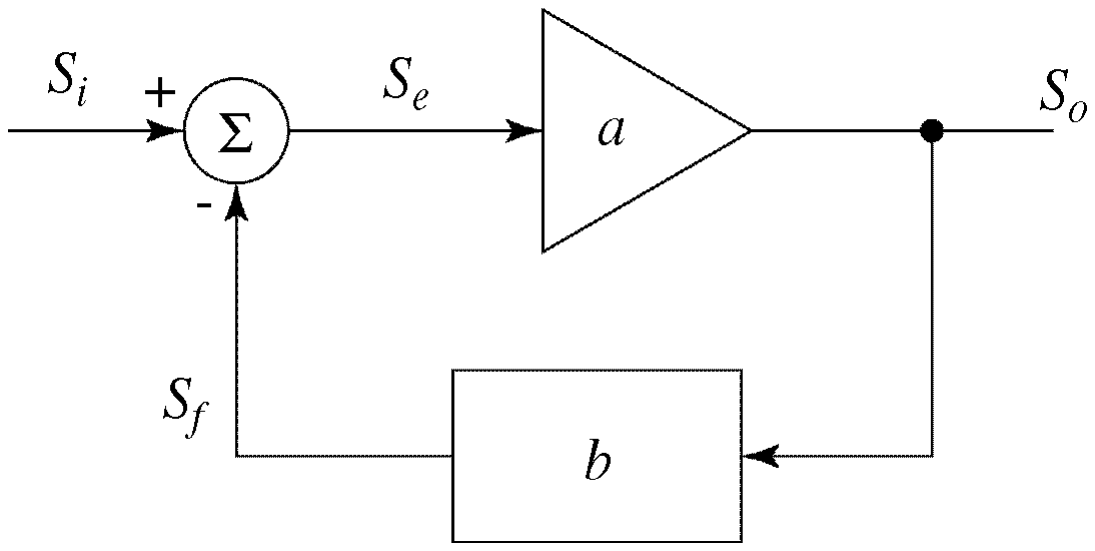
[picture p113: figure]

- As ab ∞, Se 0
- ab is called the loop gain as we saw before, so when the loop gain is large, the error is driven toward zero
( | )
(1 | )

1

e | i | f | i | o
i | e
e | i

i
e
S | S S | S bS
S b aS
S | ab | S
S S
ab

= − =−
=−
+ | =
| = +

### Feedback Control Loop

A feedback control loop uses different terminology than the amplifier just shown, but the principle is the same.
– Compare a signal fed back from the output with a reference input. Feed the resulting error into a controller that drives the plant or process to produce the desired output. The objective is to drive the error to zero.

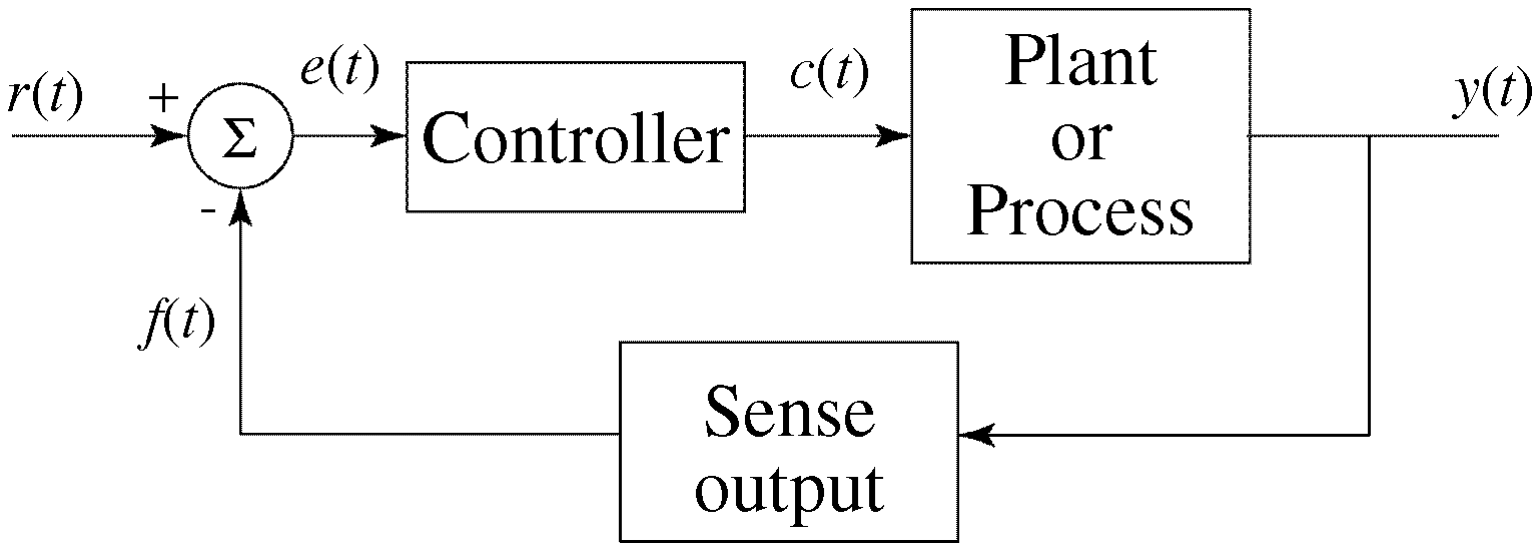
[picture p114: figure]

### Control Loop Transfer Functions

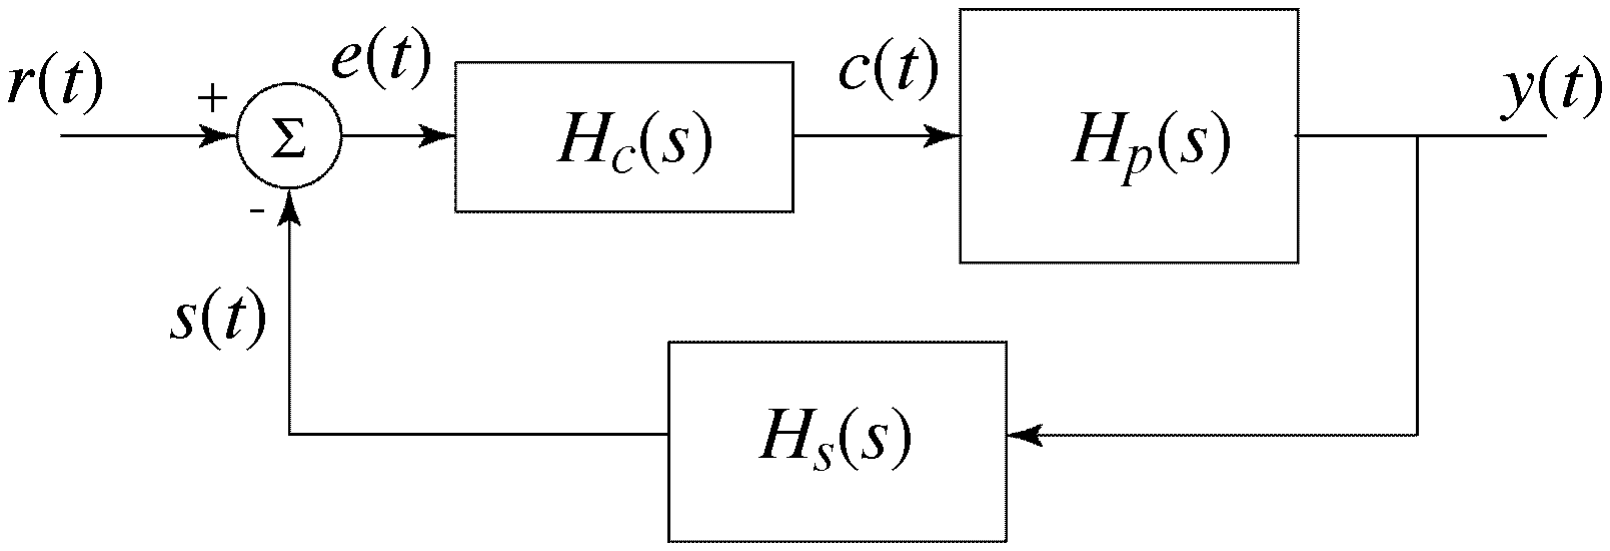
[picture p115: figure]

The overall transfer function is

denote the loop gain as

() | () () 1 | () | () ()
| | c | p
T
c | p | S

H sH s
Hs

H sH sH s = +

() | () | () () L | c | p | S s | H sH sH s =

### Control Loop Stability

- The poles of HT(s) are given by the solutions of
the characteristic equation | .
- For the system to be stable, all of the poles of HT(s) must be in the left half of the complex plane.
- There are two common ways of checking whether or not all of the poles lie in the LHP:
– By doing a Nyquist plot
– By checking the gain and phase margins
- The Nyquist plot is the more general method, but gain and phase margins are more common for amplifiers.

1 () 0 + L s =

### Nyquist Plot

- A Nyquist plot is simply a plot of the complex values of L(jω) as ω varies from −infinity to +infinity.
- The plot always has symmetry about the real axis.
- If the plot encircles the point −1+j0 in the clockwise direction, and L(s) does not have poles in the RHP, then there are closed-loop poles in the RHP and the number of times the plot encircles the point -1+j0 is equal to the number of poles in the RHP.

### Nyquist Plot Example

() | ( | )( | )
3 | 150
5 | 10 1 | 1
5 | 10
Lj | j | j | j | j

ω

ω | ω | ω | ω = | = ⎛ | ⎞⎛ | ⎞ | + | + ⎜ | ⎟⎜ | ⎟ + | + ⎝ | ⎠⎝ | ⎠

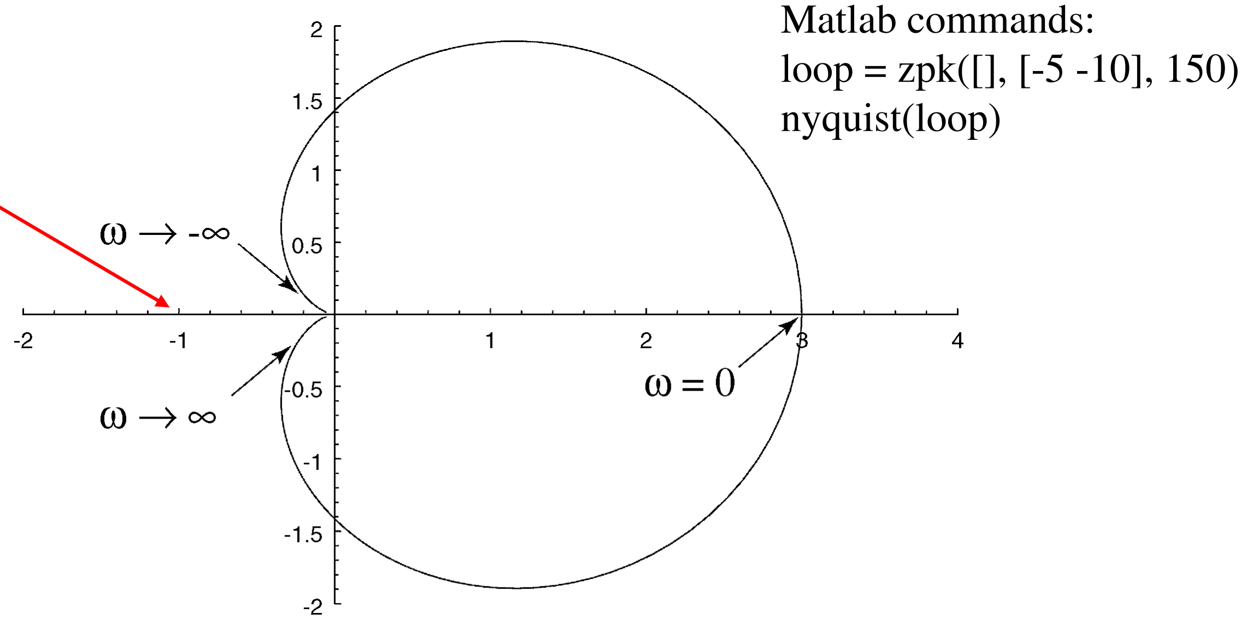
[picture p116: figure]
Matlab commands: loop = zpk([], [-5 -10], 150) nyquist(loop)

System is stable. All closed-loop poles are in the LHP

-1+j0

### 2nd Nyquist Plot Example

() ( | )( | )( | )

30
1 | 1 | 5 1 | 10 Lj | j | j | j

ω

ω | ω | ω = + | + | +

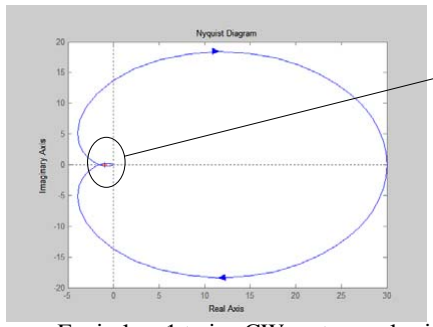
[picture p117: figure]
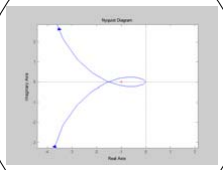
[picture p118: figure]

Encircles -1 twice CW ⇒ two poles in RHP, so unstable

Matlab commands:
loop = zpk([], [-1 -5 -10], 1500) nyquist(loop)

### Gain and Phase Margins

- A less general, but common, method for examining stability is to use a Bode plot of L(jω) and look to see how close the phase is to -180˚ when the gain is 1 (0 dB) or more.
- The method works so long as the magnitude of the phase is monotonically non-decreasing with increasing frequency.
- A common textbook goal, which is easy to do graphically, is to set the phase margin to 45˚;
PM = 45˚. A more typical number in real designs is PM = 60˚.

Definitions of Gain and Phase Margins

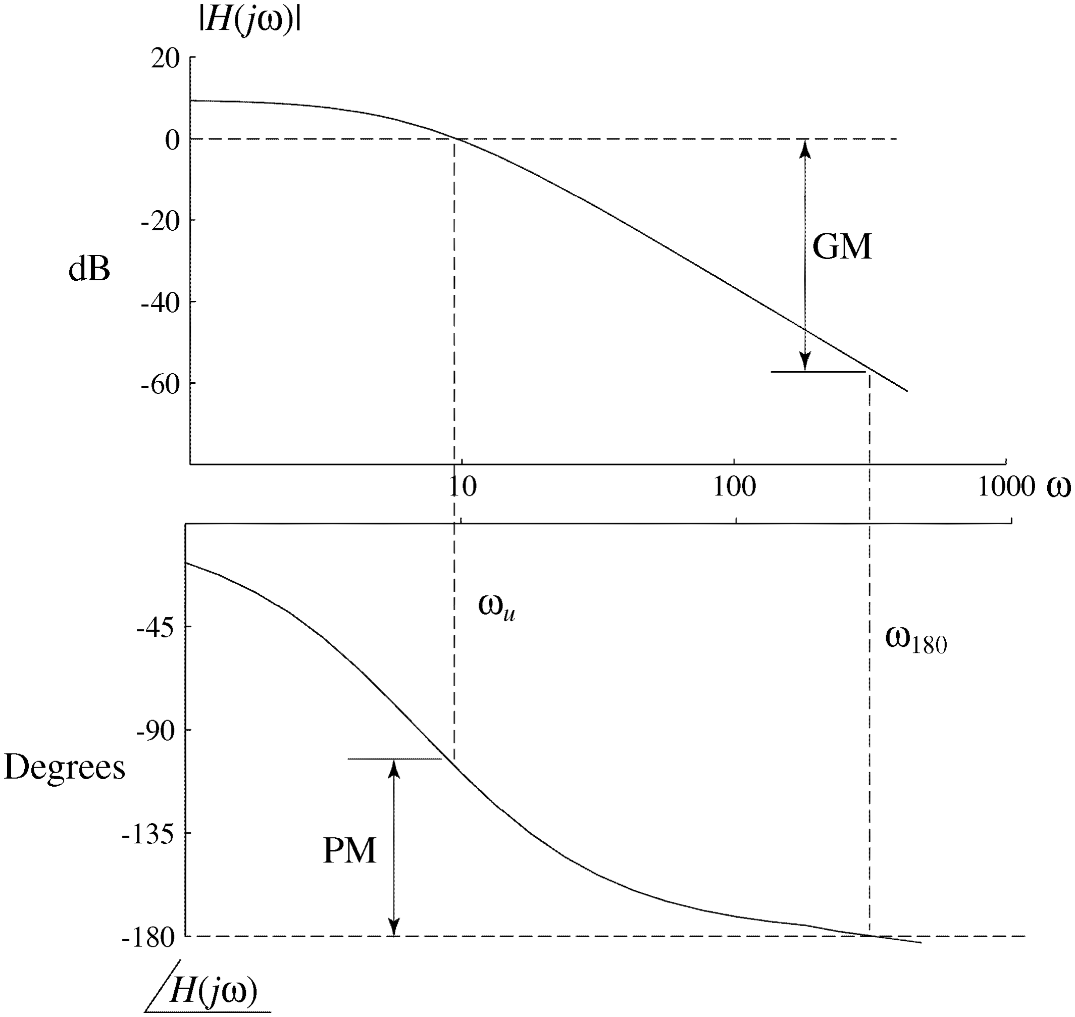
[picture p119: figure]

- The GM is the
extra gain
required to
reach 0 dB
when the phase
is -180˚
- The PM is the
extra phase
delay needed to
reach -180˚
when the gain
is 0 dB.

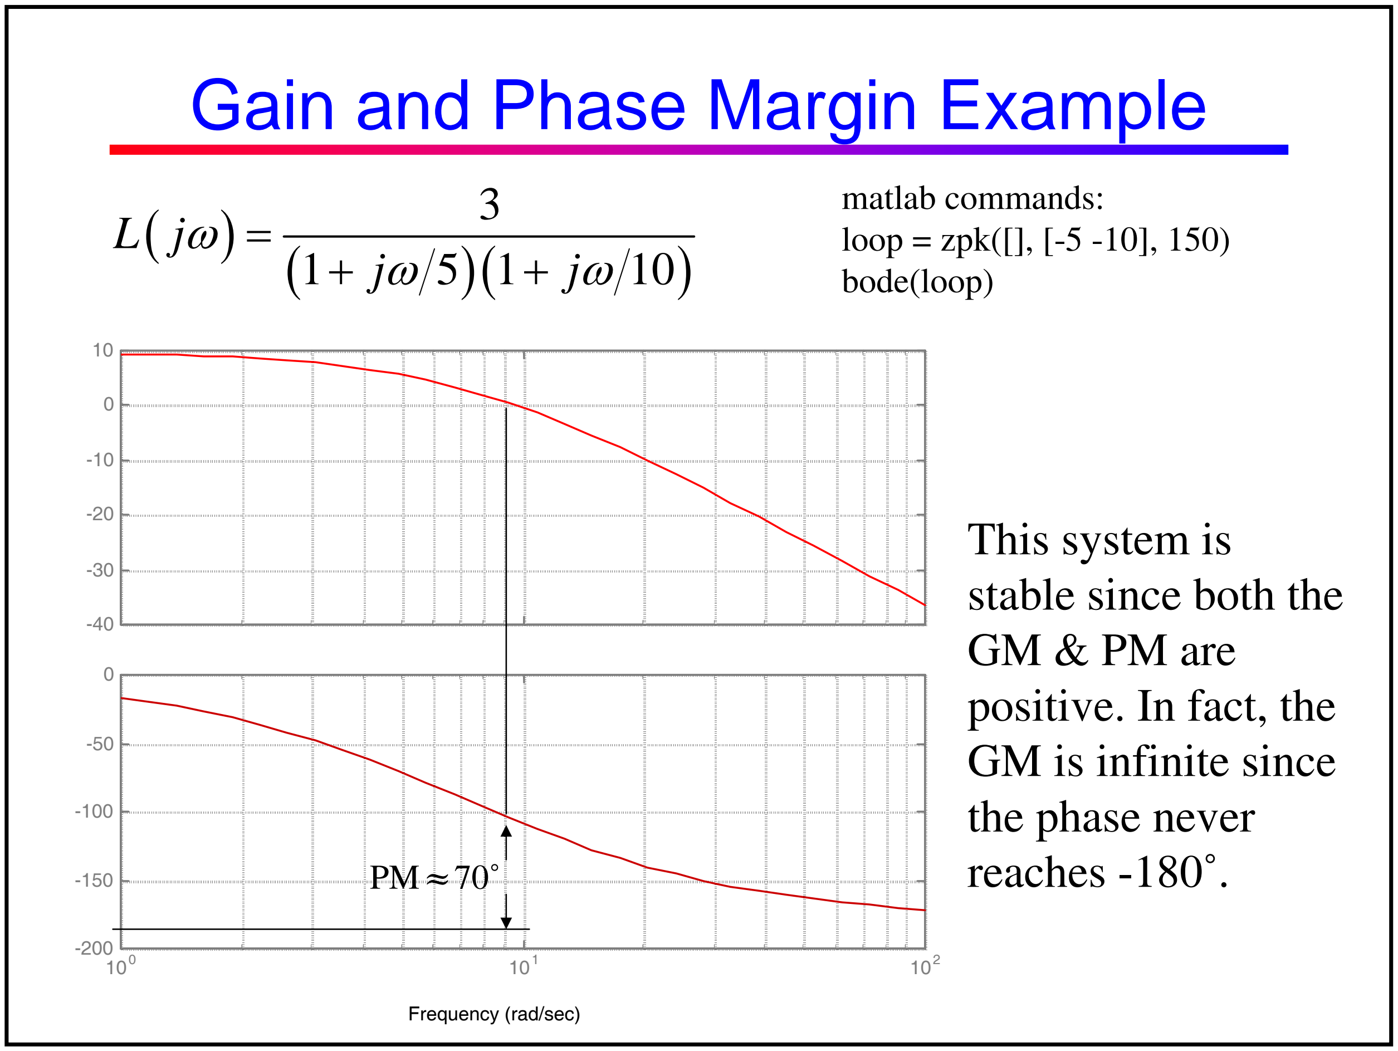
[picture p120: figure]
Gain and Phase Margin Example; Frequency (rad/sec); Bode Diagrams; This system is stable since both the GM & PM are positive. In fact, the GM is infinite since the phase never; reaches -180˚.; matlab commands: loop = zpk([], [-5 -10], 150) bode(loop)

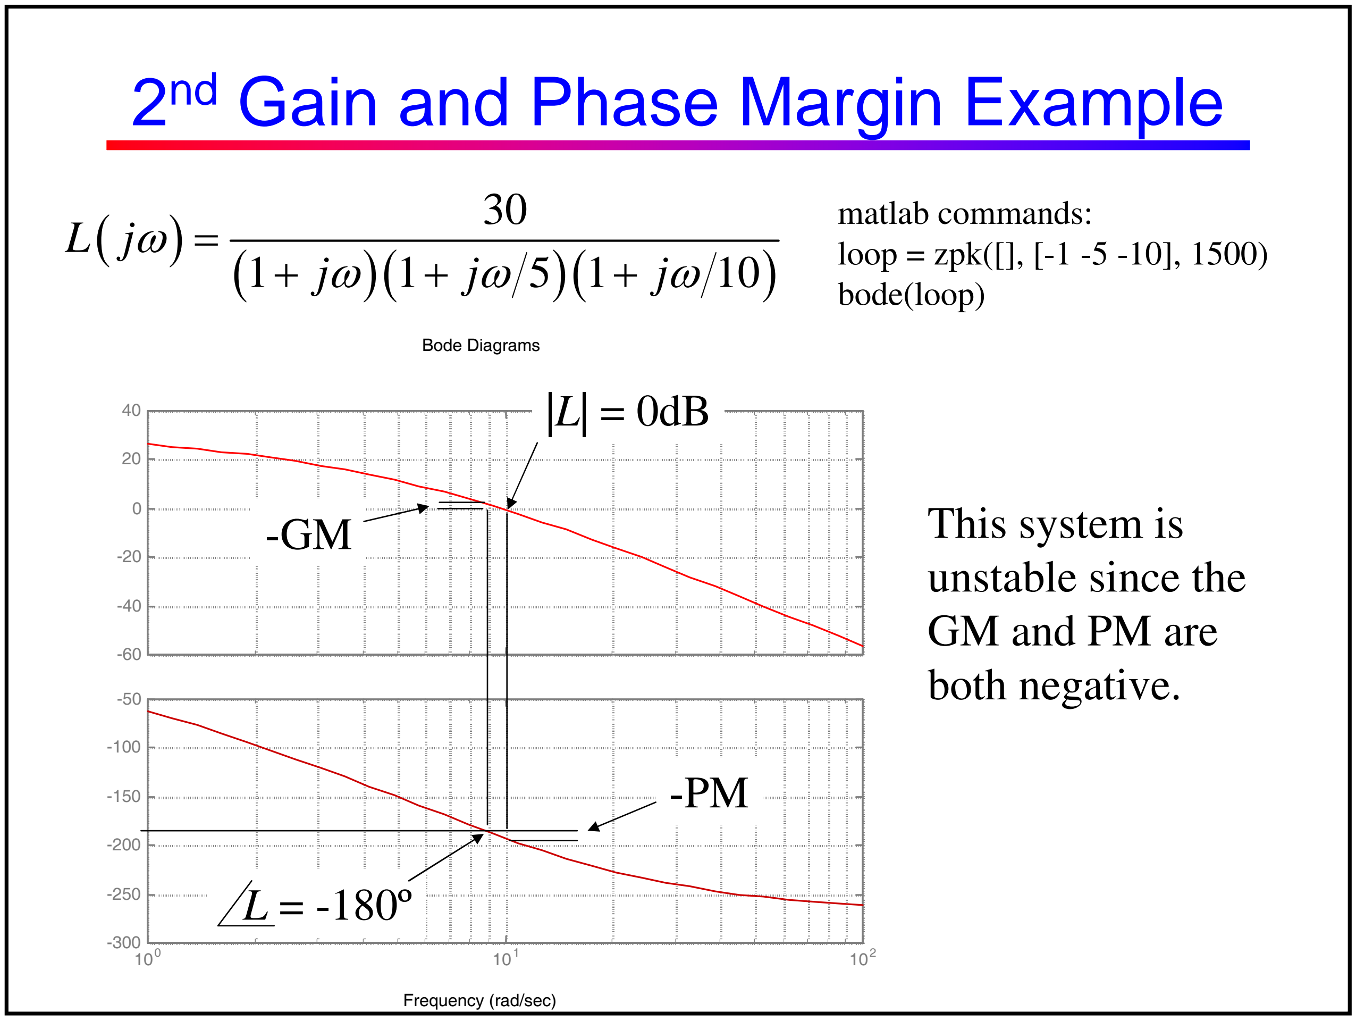
[picture p121: figure]
2nd Gain and Phase Margin Example; Frequency (rad/sec); Bode Diagrams; This system is unstable since the GM and PM are both negative.; matlab commands: loop = zpk([], [-1 -5 -10], 1500) bode(loop)

### Step Response of Unstable Loop

If the loop gain is given by

then the closed-loop step response clearly shows the instability (use open-loop gain a = 1).

() ( | )( | )( | )

30
1 | 1 | 5 1 | 10 Lj | j | j | j

ω
ω | ω | ω = + | + | +

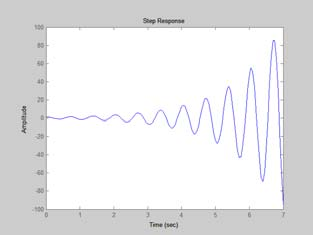
[picture p122: figure]

Matlab commands:
L = zpk([],[-1 -5 -10],1500) HT = 1/(1+L)
step(HT,0:.05:7)

### Step Response of Stable Loop

If the loop gain is given by

then the closed-loop step response clearly shows the system is stable (use open-loop gain a = 1).

() ( | )( | )

3
1 | 5 1 | 10 Lj | j | j

ω
ω | ω = + | +

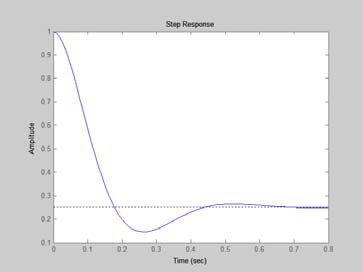
[picture p123: figure]

( 0) 14 T Hj =

This is the step response
of HT = 1/(1+L), so at
t = 0 it starts at 1, and
then the loop responds
and starts to reduce the
error. If we leave the
step input forever, it is a DC term and

### Root-Locus Plots

- We have seen that the poles of the closed-loop system are critically important in determining stability.
- We have also seen how to check stability if the loop gain is known (complete transfer function).
- One other very useful and intuitive technique allows us to examine how the closed-loop poles vary with the DC loop gain; this method is called a Root-Locus Plot.

### Root-Locus Plots; Method

- Suppose the loop gain of our system is written in the form:
- The closed-loop transfer function is then of the form:
- Now multiply the numerator and denominator by
( | )( | )( | )
( | )( | )( | )
1 | 2 | 3
1 | 2 | 3
() | sz sz | sz Ls | K
sp sp | sp
+ | + | + = | + | + | +
( | )( | )( | )
( | )( | )( | )
1 | 2 | 3
1 | 2 | 3

() ()

1

Ns Hs
sz sz sz K
sp sp sp
= | + | + | +
+
+ | + | +
(sp sp sp + 1 | 2 | 3 )( + | + )( | )

Root-Locus Plots; Method cont.

- We obtain:
- The closed-loop poles are given by the solutions of the characteristic equation:
( | )( | )( | )
( | )( | )( | ) ( | )( | )( | )
1 | 2 | 3
1 | 2 | 3 | 1 | 2 | 3
() () | Ns s p s p s p Hs
s p s p s p | Ks z s z | s z
+ | + | + = + | + | + | + | + | + | +
( | )( | )( | ) ( | )( | )( | ) 1 | 2 | 3 | 1 | 2 | 3 s p s p | s p | Ks z s z | s z + | + | + | + | + | + | + | = 0

NOTE: These are the poles of L(s), and these are the zeros!

Root-Locus Plots; Method cont.

- The solutions of:
- Are given by:
– The poles of L(s) when K = 0
– The zeros of L(s) as K approaches infinity
- Therefore; the locus of the poles of H(s) starts on the poles of L(s) and ends on the zeros of L(s).
( | )( | )( | ) ( | )( | )( | ) 1 | 2 | 3 | 1 | 2 | 3 s p s p | s p | Ks z s z | s z + | + | + | + | + | + | + | = 0

Root-Locus Plots; Method cont.

- In addition to starting on the poles of L(s) and ending on the zeros of L(s), the locus of the poles of H(s) must only include points that satisfy the characteristic equation:
- In other words, these points must satisfy two conditions:

and

1 () 0 + L s =

Ls() | 1=
∠L( ) | 180 s =± | °

Root-Locus Plots; Method cont.

- Note that with
- The magnitude condition becomes
(assume K > 0):

which depends on the value of K. We will not use this condition to construct the locus, but it will allow us to find a specific point on the locus if we want to later.

( | )( | )( | )
( | )( | )( | )
( | )( | )( | )
( | )( | )( | )
1 | 2 | 3 | 1 | 2 | 3
1 | 2 | 3 | 1 | 2 | 3
1 sz sz | sz | sz sz | sz
K | K
sp sp sp | sp sp sp
+ | + | + | + | + | + = | = + | + | + | + | + | +
( | )( | )( | )
( | )( | )( | )
1 | 2 | 3
1 | 2 | 3
() | sz sz | sz Ls | K
sp sp | sp
+ | + | + = | + | + | +

Root-Locus Plots; Method cont.

- Also note that with
- The angle condition becomes (assume K > 0):

which is the condition we will use to find the locus.

( | )( | )( | )
( | )( | )( | )
( | )( | )( | ) ( | )( | )( | )
1 | 2 | 3
1 | 2 | 3
1 | 2 | 3 | 1 | 2 | 3 | 180
sz sz | sz K
sp sp sp
sz sz | sz | sp sp | sp
⎛ | ⎞ + | + | +
∠⎜ | ⎟ + | + | + ⎝ | ⎠
=∠ + | + | + | −∠ + | + | + | =± | °
( | )( | )( | )
( | )( | )( | )
1 | 2 | 3
1 | 2 | 3
() | sz sz | sz Ls | K
sp sp | sp
+ | + | + = | + | + | +

### Plotting the Root Locus

- We can now describe a procedure for plotting a root locus:
- The locus begins at the poles of the loop gain and ends on the zeros (we must include zeros at infinity)
- Any point in the plane that satisfies the angle condition is part of the locus; i.e., the sum of the angles of the vectors from the loop-gain zeros to the point, minus the sum of the angles of the vectors from the loop-gain poles to the point must be an odd integer multiple of 180º.

### Root Locus Example

- Suppose we have:
- This transfer function has two zeros at infinity. They will contribute zero phase to any finite point in the plane. Therefore, the locus will contain those points for which the sum of the angles of the two vectors from the poles to the point is ±180º.
( | )( | ) 1 | 2
() | K Ls
sp sp = + | +

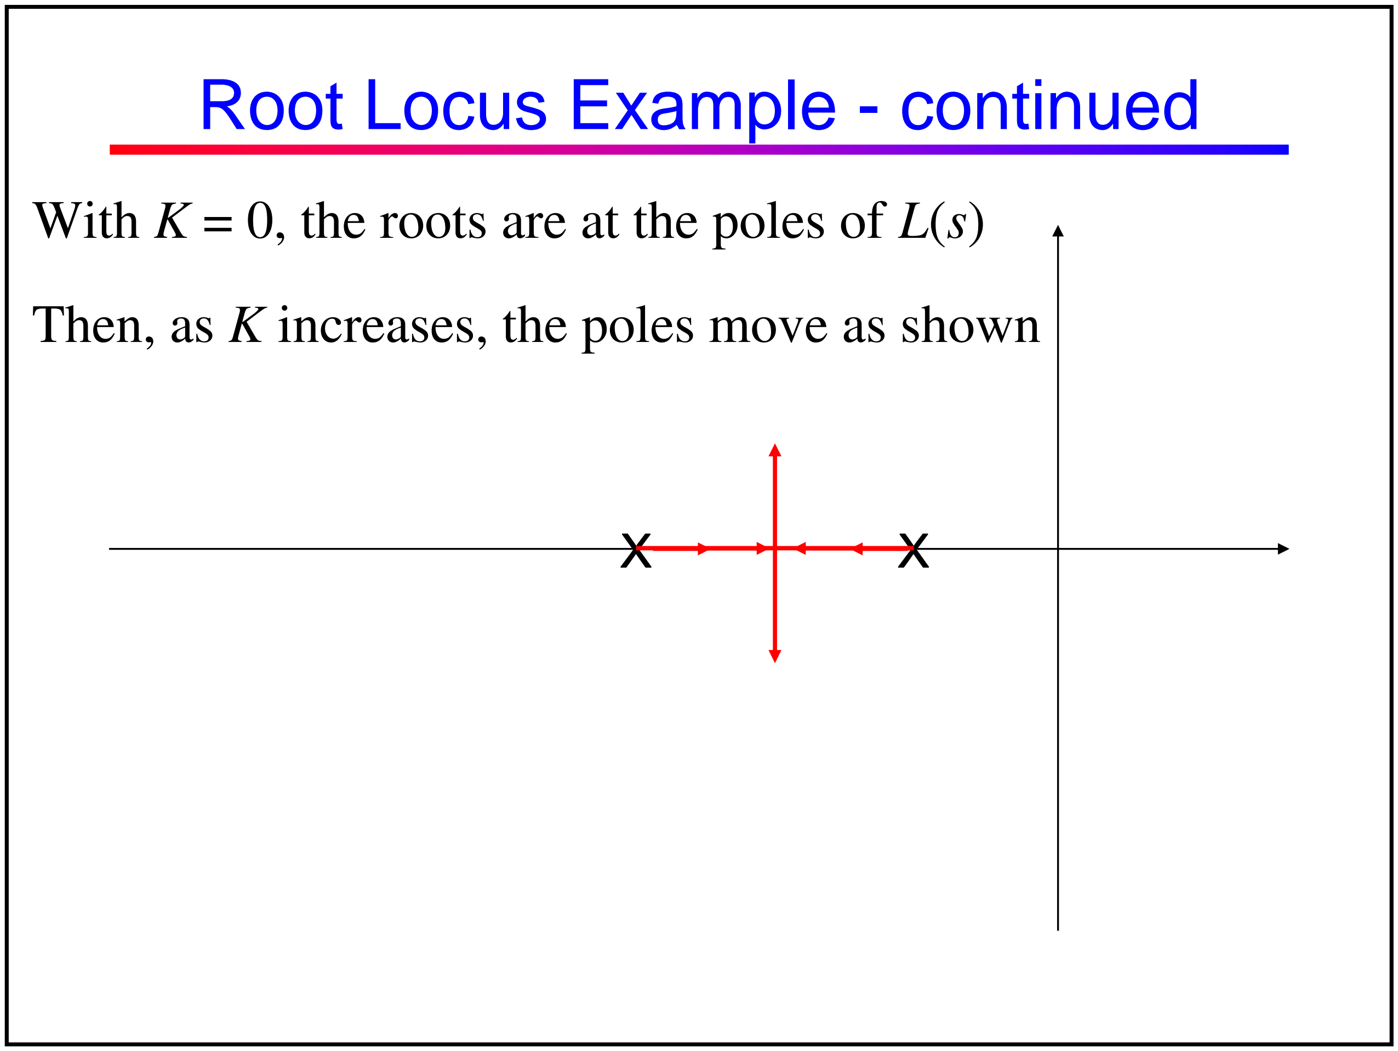
[picture p124: figure]
Root Locus Example - continued

With K = 0, the roots are at the poles of L(s) Then, as K increases, the poles move as shown

### Root Locus Example

- Now suppose we have:
- This transfer function has three zeros at infinity. They will contribute zero phase to any finite point in the plane. Therefore, the locus will contain those points for which the sum of the angles of the three vectors from the poles to the point is 180º.
- Because of the added third pole, the complex part of the locus will bend to the right to keep the total phase of the three vectors equal to 180º.
( | )( | )( | ) 1 | 2 | 3
() | K Ls
sp sp sp = + | + | +

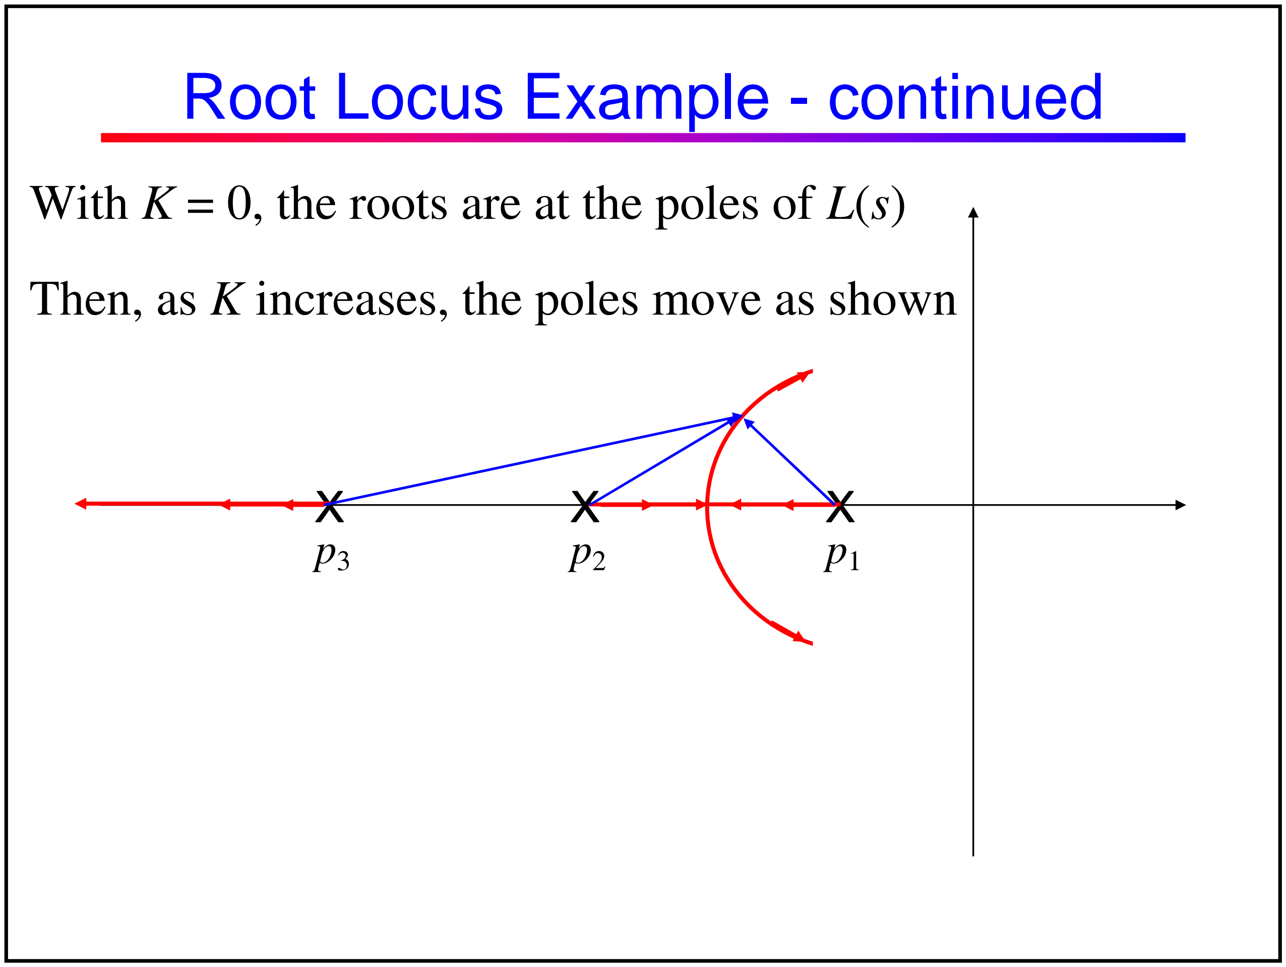
[picture p125: figure]
Root Locus Example - continued

With K = 0, the roots are at the poles of L(s) Then, as K increases, the poles move as shown

### Root Locus with Matlab

() ( | )( | )( | )

30
1 | 1 | 5 1 | 10 Lj | j | j | j

ω
ω | ω | ω = + | + | +

Matlab commands:
loop = zpk([], [-1 -5 -10], 1500) rlocus(loop)

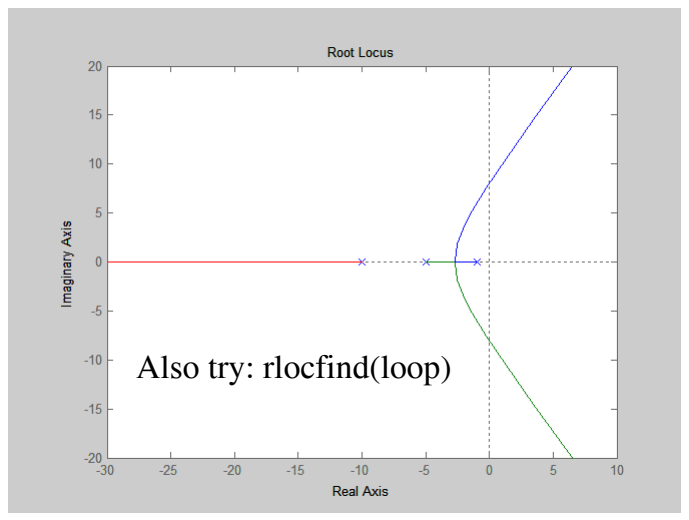
[picture p126: figure]
Also try: rlocfind(loop)
