ahsalohcin/GP-Team-8-/ihab/GrandPrIEEEE_2017-master/GrandPrIEEEE_2017-master/H-Bridge/Drive Modes/Sign-Magnitude Low-side.PNG

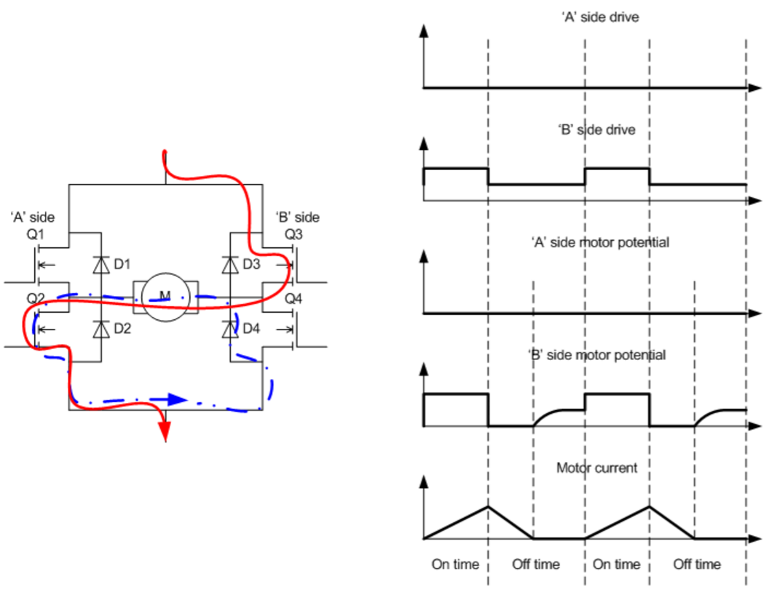
ihab/GrandPrIEEEE_2017-master/GrandPrIEEEE_2017-master/H-Bridge/Drive Modes/Sign-Magnitude Low-side.PNG
