ahsalohcin/GP-Team-8-/camera_mount_2016/base.SLDPRT

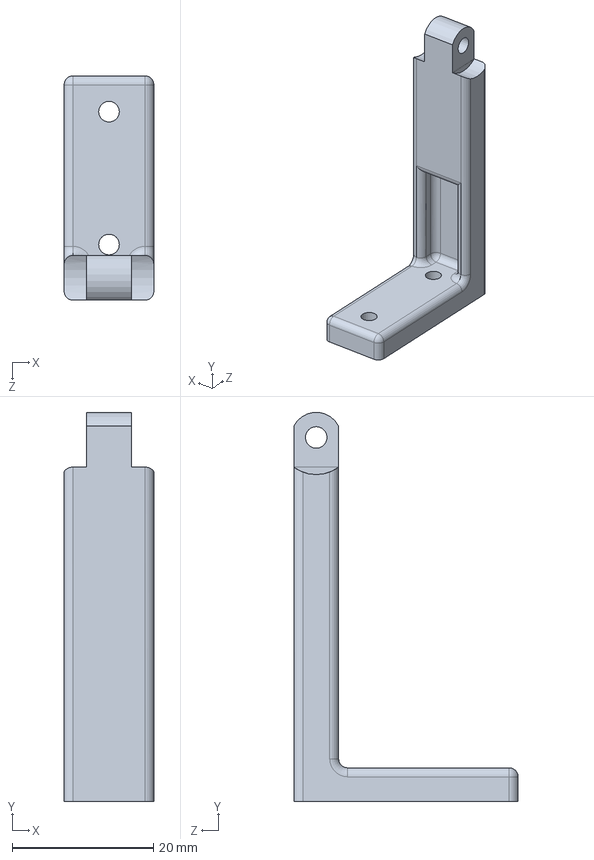
[picture p148: CAD file, 2017-04-13]
camera_mount_2016/base.SLDPRT
12.7 x 55.0 x 31.8 mm
