ahsalohcin/GP-Team-8-/speedometer/2_mill_errorv3/stick right 2 mill.SLDPRT

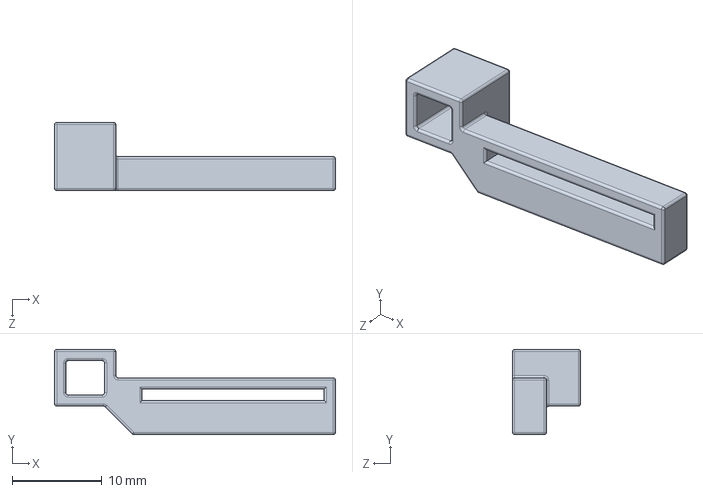
[picture p149: CAD file, 2017-04-16]
speedometer/2_mill_errorv3/stick right 2 mill.SLDPRT
31.4 x 9.52 x 7.62 mm
