ahsalohcin/GP-Team-8-/speedometer/2_mill_errorv3/pin 4 mill.SLDPRT

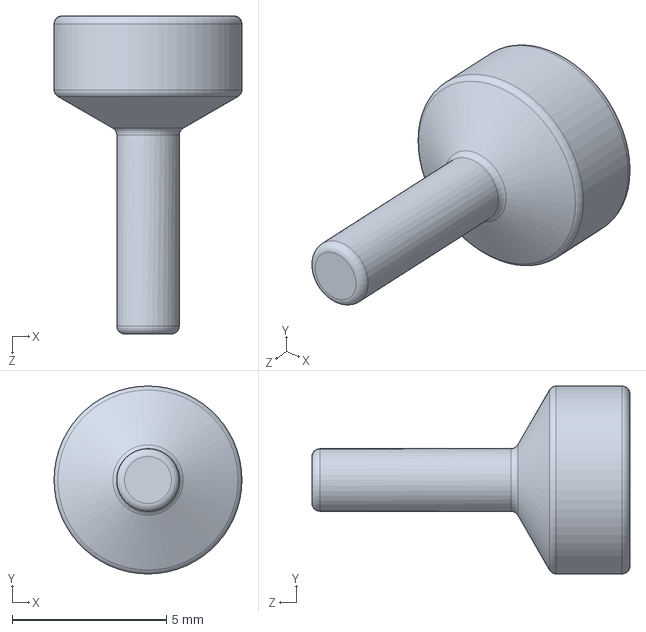
[picture p150: CAD file, 2017-04-16]
speedometer/2_mill_errorv3/pin 4 mill.SLDPRT
6.10 x 6.10 x 10.3 mm
