ahsalohcin/GP-Team-8-/speedometer/pin nominal.SLDPRT

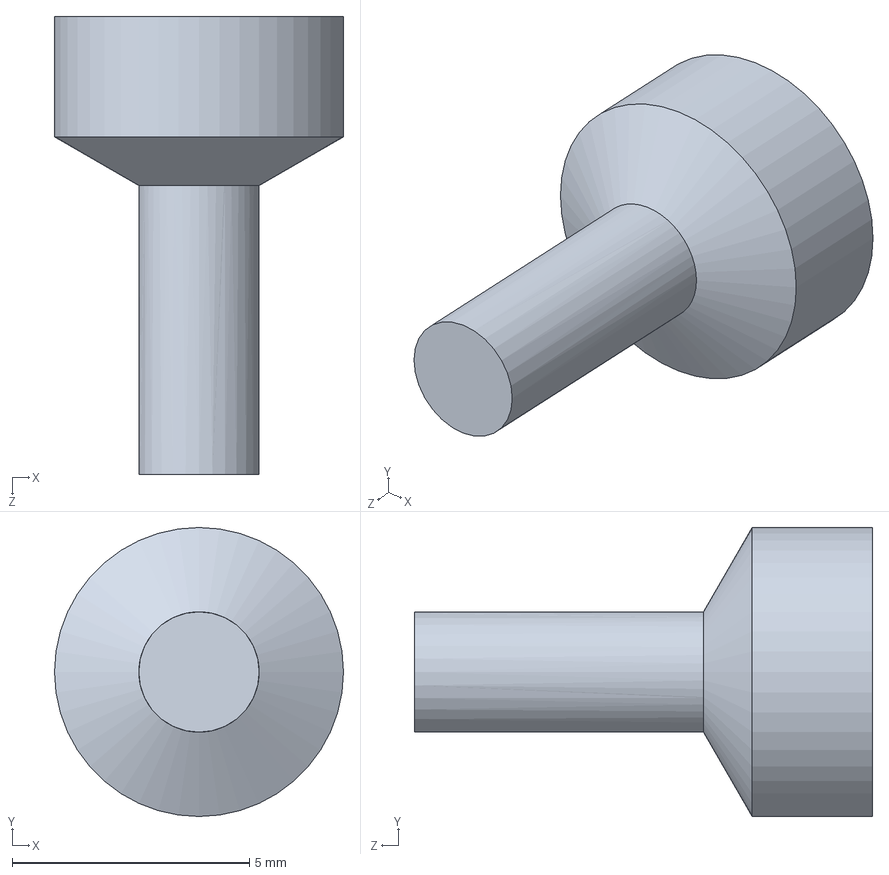
[picture p151: CAD file, 2017-02-12]
speedometer/pin nominal.SLDPRT
6.10 x 6.10 x 9.66 mm
