ahsalohcin/GP-Team-8-/speedometer/2_mill_errorv3/mount 2 mill.SLDPRT

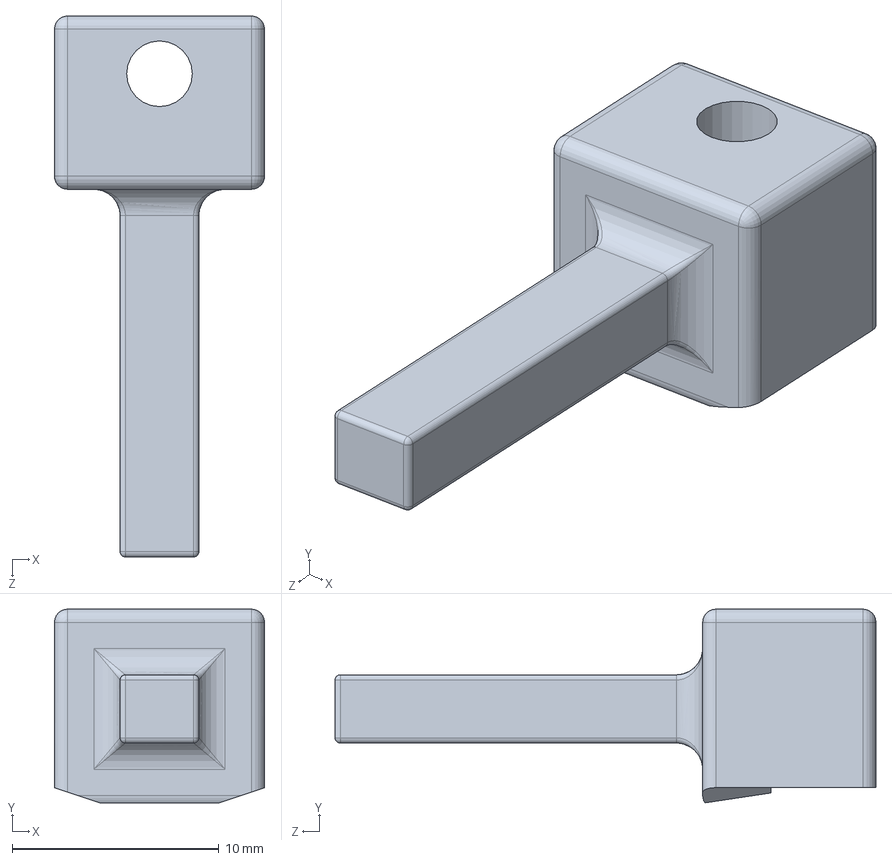
[picture p152: CAD file, 2017-04-16]
speedometer/2_mill_errorv3/mount 2 mill.SLDPRT
10.2 x 9.37 x 26.2 mm
