ahsalohcin/GP-Team-8-/hardware/sim/test.asc

C1: cap; 0.001p
D1: diode
L1: ind; 1
M1: nmos; PSMN0R930YLD
R1: res; 5
V1: voltage; 10; Rser=1
V2: voltage; 1
V3: voltage; PULSE(0 10 0 1m 1m 2 10 2)
Named nets: 0
.tran 4
